butterrsoft/GyrSync/Code/main.c

/*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
 * THE SOFTWARE IS PROVIDED "AS IS", WITHOUT WARRANTY OF ANY KIND, EXPRESS OR
 * IMPLIED, INCLUDING BUT NOT LIMITED TO THE WARRANTIES OF MERCHANTABILITY,
 * FITNESS FOR A PARTICULAR PURPOSE AND NONINFRINGEMENT. IN NO EVENT SHALL THE
 * AUTHORS OR COPYRIGHT HOLDERS BE LIABLE FOR ANY CLAIM, DAMAGES OR OTHER
 * LIABILITY, WHETHER IN AN ACTION OF CONTRACT, TORT OR OTHERWISE, ARISING FROM,
 * OUT OF OR IN CONNECTION WITH THE SOFTWARE OR THE USE OR OTHER DEALINGS IN
 * THE SOFTWARE.
 */

/*
 * GyrSync dongle -- AVR32EB14. Composite sync combiner/converter.
 *
 * Built and verified with avr-gcc 16.1.0 (ZakKemble build), which has
 * avr32eb14/eb20 device support. Clean under -Wall -Wextra; also builds
 * for avr32eb20 unchanged, via `make MCU=avr32eb20`.
 *
 * ONE BUILD. There are no compile-time variants: no EXTRA, no
 * diagnostic switches, no alternative make targets that produce a
 * different image. `make flash` is the whole of it. The diagnostics
 * this file used to carry did their job and were removed with the
 * questions they answered -- and with them the class of fault they kept
 * causing, where a build selected on a command line reached the bench
 * without anything on the part to say which one it was.
 *
 * =====================================================================
 * WHERE THINGS LIVE
 * =====================================================================
 *
 * THE PIN MAP IS IN pins.h, AND ONLY THERE. It used to be duplicated in
 * this comment, and the copy drifted -- it described the pre-rotation
 * wiring, with DDC on pins 4/5 and Csync on pin 9, long after the
 * oscillator took PA0 and moved all of it. A map that disagrees with
 * itself is worse than no map, so there is one.
 *
 *   pins.h    every pin this project touches, named once
 *   clock.h   CLKCTRL, the PLL, the external oscillator
 *   tick.h    TCF0, the 4kHz interrupt and the millisecond tick
 *   evsys.h   all six event channels, and every event user
 *   ccl.h     all four LUTs, every truth table, CCLROUTEA
 *
 * Each of those modules is the SINGLE OWNER of its registers. That is
 * not tidiness: nearly every bug this firmware has had at the hardware
 * level was two writers on one register, and the split is what makes a
 * second writer a link error rather than a bench round.
 *
 * =====================================================================
 * PERIPHERAL ALLOCATION
 * =====================================================================
 *
 *   TCB0   Hsync capture, FRQ mode: one period measurement per line,
 *          restarted by the event system. Level 1 -- the only interrupt
 *          in this design that cannot be late, because Mode V counts
 *          lines and a lost count moves the emitted Vsync.
 *   TCB1   one timer, three jobs, one owner -- see tcb1_reevaluate().
 *          Mode S's pulse reshaping, the Hsync width measurement, and
 *          Mode FO's sub-line field delay.
 *   TCE0   the H offset. Restarted by Hsync in hardware, pulse placed
 *          by CMP0/CMP1 with the 8x high-resolution extension.
 *   TCF0   the 4kHz housekeeping interrupt: the millisecond tick and
 *          the Blink LED's software PWM.
 *   TWI0   the DDC/EDID client, at 0x50 with 0x30 also ACKed.
 *   CCL    the combiner and everything feeding it.
 *   RTC    unused.
 *
 * =====================================================================
 * THE Rev. A0 WRITE-LOSS ERRATUM, AND WHY NO WORK-AROUND APPEARS BELOW
 * =====================================================================
 *
 * A store to an address >= 0x40 followed by a store below 0x40 loses
 * the second write. Everything below 0x40 on this part is VPORTA/C/D/F
 * (0x00-0x17), GPR (0x1C) and the CPU block (0x30, which holds SREG and
 * the stack pointer). Every peripheral this firmware touches lives at
 * or above 0x40 -- PORT is at 0x0400, CCL at 0x01C0, and so on.
 *
 * So the rule is simply: NEVER TOUCH VPORT OR GPR. Use PORTx.OUTSET and
 * PORTx.OUTCLR, which are above the boundary and cannot be affected.
 * Nothing here needs VPORT's single-cycle access anyway -- the sync
 * path is combinational logic in the CCL, not the CPU.
 *
 * The one remaining sub-0x40 write is restoring SREG, which avr-gcc
 * emits as OUT -- itself the erratum's documented work-around. That is
 * a compiler behaviour rather than a guarantee, so `make lst` exists to
 * check it, and it should be re-checked whenever the toolchain changes.
 *
 * Checked on avr-gcc 16.1.0 for this build: every SREG access is
 * OUT 0x3f, CCP is OUT 0x34, the stack pointer is OUT 0x3d/0x3e, and
 * the only ST instructions in the image are the C runtime's .data copy
 * and .bss clear (targeting RAM at 0x7400+) and two inside
 * eeprom_update_byte (targeting the mapped EEPROM at 0x1400+ and
 * NVMCTRL at 0x1000+). Every one of those is at or above 0x40, so the
 * erratum's trigger condition does not occur anywhere in the build.
 */

#define F_CPU 20000000UL
#include "pins.h"
#include "tick.h"
#include "clock.h"
#include "evsys.h"
#include "ccl.h"

#include <avr/io.h>
#include <avr/interrupt.h>
#include <avr/eeprom.h>
#include <avr/cpufunc.h>   /* _PROTECTED_WRITE */
#include <string.h>        /* memcpy, for the EDID shadow rebuild */

/* THERE IS NO GENERATED EDID HEADER ANY MORE. edid_data.h is deleted.
 * The six images are the six .bin files, pulled straight into .rodata
 * by the assembler -- see the .incbin block in the DDC/EDID section
 * below, which is also where the build-time size rules live. */

/* ===================================================================
 * Modes
 * =================================================================== */

#define MODE_1  1
#define MODE_2  2
#define MODE_3  3
#define MODE_4  4
#define MODE_5  5
#define MODE_S  6

/* ===================================================================
 * Hsync acceptance windows, in TCB0 counts at CLK_PER
 * ===================================================================
 *
 * The fast and slow windows are carried over from the ATtiny824
 * unchanged. They are about 30% wide in frequency, so a half-percent of
 * oscillator error is nowhere near their edges and there is nothing to
 * recalibrate.
 *
 * Mode 4's window is the exception and is the one thing here that MUST
 * be re-measured on this part. It spans 24450-25450Hz, four percent
 * wide, which is close enough to the oscillator's own error that the
 * ATtiny824 build had to derive it from a bench measurement of that
 * chip -- ~19.897MHz rather than the nominal 20MHz -- before Mode 4
 * would accept a real 24960Hz source reliably.
 *
 * So Mode 4's edges are computed from F_PER_MEASURED rather than
 * written as counts, and nothing else in the file depends on the value.
 *
 * ON THE EXTERNAL OSCILLATOR THIS IS EXACT AND NEEDS NO CALIBRATION.
 * clock_init() runs the PLL from the 20MHz crystal module on pin 4, so
 * CLK_PER is 20MHz to the oscillator's 50ppm -- four hundred times
 * tighter than the four-percent window, and 20000000 is simply right.
 *
 * IT IS NOT EXACT ON THE FALLBACK PATH. If the oscillator is absent or
 * dead, clock_init() resets once and the second boot runs the PLL from
 * OSCHF instead, whose error is comparable to the width of this window
 * -- which is exactly why the ATtiny824 build had to measure its part
 * at ~19.897MHz before Mode 4 would accept a real 24960Hz source. A
 * unit that has fallen back may therefore reject Mode 4 sources it
 * should take. That is a consequence of a missing part rather than
 * something to trim this constant for: with the oscillator fitted,
 * leave it at 20000000.
 */
#define F_PER_MEASURED    20000000UL   /* <-- re-measure on the bench */

/* Boundaries land OUTSIDE the stated range in both directions: floor on
 * the low count, ceiling on the high one. An exactly-computed edge
 * rejects a legitimate source that misses it by a handful of counts. */
#define COUNTS_FLOOR(hz)  ((uint16_t)( F_PER_MEASURED / (hz)))
#define COUNTS_CEIL(hz)   ((uint16_t)((F_PER_MEASURED + (hz) - 1) / (hz)))

#define HSYNC_FAST_MIN_COUNTS   615   /* 32500Hz */
#define HSYNC_FAST_MAX_COUNTS   656   /* 30500Hz */
#define HSYNC_SLOW_MIN_COUNTS  1176   /* 17000Hz */
#define HSYNC_SLOW_MAX_COUNTS  1333   /* 15000Hz */
#define HSYNC_M4_MIN_COUNTS    COUNTS_FLOOR(25450UL)
#define HSYNC_M4_MAX_COUNTS    COUNTS_CEIL(24450UL)

_Static_assert(HSYNC_M4_MIN_COUNTS > HSYNC_FAST_MAX_COUNTS,
               "Mode 4 window overlaps the fast window");
_Static_assert(HSYNC_M4_MAX_COUNTS < HSYNC_SLOW_MIN_COUNTS,
               "Mode 4 window overlaps the slow window");

#define W_FAST 0x01
#define W_SLOW 0x02
#define W_M4   0x04

/* Which windows each mode accepts. One table to check against the mode
 * documentation, rather than a branch chain that recomputes the same
 * three tests and then picks between them. */
static const uint8_t mode_windows[MODE_S + 1] = {
    0,                        /* index 0 unused */
    W_SLOW,                   /* MODE_1  15-17kHz */
    W_FAST,                   /* MODE_2  30.5-32.5kHz */
    W_FAST | W_SLOW,          /* MODE_3  both */
    W_M4,                     /* MODE_4  narrow ~25kHz */
    W_FAST | W_SLOW | W_M4,   /* MODE_5  all three */
    W_FAST | W_SLOW,          /* MODE_S  both; divides the fast one,
                               * from increment 3 */
};

/* ===================================================================
 * Mode S divide-by-2, and the CCL role swap
 * ===================================================================
 *
 * Mode S accepts both the slow and the fast window. On a slow source it
 * passes Hsync through like any other mode. On a fast one it halves it,
 * so an unbidden 31kHz fallback still shows on a 15kHz CRT.
 *
 * THE DIVIDER OUTPUT IS A TIMING REFERENCE, NOT A SYNC SIGNAL. A
 * flip-flop dividing by two produces a 50% square wave -- about 32us
 * high and 32us low at the resulting 15.7kHz -- which no sync separator
 * will lock to. Each rising edge of it therefore fires a one-shot that
 * emits a fixed-width pulse, and that pulse is what reaches the
 * combiner. This is easy to miss because the divider looks perfect on a
 * logic analyser and fails only at the display.
 *
 * RISING EDGES ONLY, which is worth stating because section 4 of the
 * spec says "each of its edges triggers a one-shot". Taken literally
 * that undoes the division: the square wave has 15.7k rising and 15.7k
 * falling edges per second, so firing on both puts 31.5k pulses per
 * second back on the output. TCB1 is left with EVCTRL.EDGE clear, which
 * triggers on positive edges only and gives one pulse per output line.
 *
 * 4.0us is close to the 4.7us analogue standard and comfortably inside
 * what a 15kHz separator expects. It is a fixed count rather than a
 * fraction of the period because at this point the output rate is known
 * to be in the 15-17kHz window by construction.
 *
 * The counter runs at CLK_PER, so one count is 50ns.
 */
#define RESHAPE_PULSE_COUNTS     80          /* 80 x 50ns = 4.0us */

_Static_assert(RESHAPE_PULSE_COUNTS * 50UL < 10000UL,
               "reshape pulse is wider than a sync pulse should ever be");

/* Which shape the CCL is currently built in. The boundary between the
 * two is NOT the mode -- it is Mode S's own fast/slow decision, so the
 * swap happens at the rate threshold rather than at a mode change.
 *
 * REWRITTEN FOR THE ROTATION. This block described the pre-rotation
 * assignment, where LUT1 was the combiner and LUT2 held the two
 * alternating jobs. Since the oscillator took PA0 and DDC took PC3, the
 * only CCL output pin left is PD6, so LUT2 is the OUTPUT STAGE and is
 * the combiner in every role. What alternates is LUT0/LUT1 and LUT3.
 * ccl.c's header carries the full table.
 *
 *   CCL_ROLE_PASSTHRU  LUT2 combines, taking Hsync straight from the
 *                      pin by event. LUT1 is the restart edge sense and
 *                      LUT3 the reconstruction XOR, both built but only
 *                      consulted by TCE0. Every mode except
 *                      Mode-S-on-a-fast-source.
 *   CCL_ROLE_RECON     the same, except LUT2 takes its H input from
 *                      LUT3 by LINK -- the rebuilt, offset pulse
 *                      instead of the pin. Engaged only when the H
 *                      offset is off centre.
 *   CCL_ROLE_DIVIDE    LUT0+LUT1 become SEQ0's J-K, halving a fast
 *                      source; LUT2 takes the reshaped pulse from TCB1
 *                      on IN2; LUT3 is disabled. Mode S on a fast
 *                      source only, and the H offset stands down here
 *                      -- the divider wins because without it there is
 *                      no picture at all, whereas without the offset
 *                      there is merely a mispositioned one.
 */
/* ccl_role_t moved to ccl.h with the module that acts on it. */

/* ===================================================================
 * H offset (increment 4b)
 * ===================================================================
 *
 * The reconstruction is the XOR of TCE0's WO0 and WO1 -- a pulse
 * spanning CMP0 to CMP1, so BOTH its edges come from compare matches
 * and neither is at BOTTOM. That is what earns the high-resolution
 * extension on both edges rather than one, and diag1 confirmed on
 * silicon that the two are stable relative to each other within 10-20ns.
 *
 * ENGAGED ONLY WHEN THE OFFSET IS OFF-CENTRE, and only while the
 * genlock holds lock. At the neutral setting, and any time lock is
 * lost, LUT1 goes back to the pin. A genlock failure therefore costs
 * the offset, not the picture -- which is the right way round for a
 * device whose whole job is to produce Csync.
 *
 * STEP SIZE is derived from the measured period rather than fixed, so a
 * step means the same fraction of a line at any rate, as section 6.4
 * requires. One step is the period in hi-res units divided by 1024:
 * 9 units at 15.7kHz, which is 56ns, about two thirds of a pixel on a
 * 640-wide active area. 114 steps either side of centre is +/-10.1% of
 * a line.
 *
 * The spec asks for +/-12% and this is a little less. The history is
 * that the range came down and the resolution went up together: 61
 * steps of 244ns originally, then 121 of 119ns, then 181 of 56ns at
 * +/-8%, now 229 of 56ns at +/-10% -- the step held while the travel
 * was extended. Sub-pixel throughout, and 229 still fits the byte the
 * setting is stored in.
 *
 * 228 divides exactly by the UI stride of 6, so the sweep lands on both
 * ends AND on centre, where the offset switches itself off.
 */
#define H_OFFSET_STEPS    229
#define H_OFFSET_DEFAULT  114

#define HOFF_STEP_SHIFT   10    /* step = per_hires >> 10 */

/* Steps moved per short press in Mode H. One step is 56ns -- two thirds
 * of a pixel -- which is the right STORED resolution but far too fine to
 * sweep by hand: 180 presses end to end. Six steps is 337ns a press,
 * about four pixels, and 180 divides exactly by 6 so the range lands on
 * both ends AND on centre, where the offset switches itself off.
 *
 * Keeping the stored value fine and the UI coarse means the feel can be
 * retuned without touching the placement arithmetic or the EEPROM
 * format. */
#define HOFF_UI_STRIDE    6

/* MEASURED CHARACTERISTIC: THE NEGATIVE SIDE'S FLOOR WAS THE
 * OSCILLATOR, AND IS NOT ANY MORE. Both halves are worth keeping --
 * the first is why the crystal was fitted, the second is what it did.
 *
 * ON OSCHF. Emitted edge spread against how far after the restart the
 * pulse is placed, measured on Csync with delayed sweep and infinite
 * persistence, source jitter independently confirmed at 5ns:
 *
 *     6.25us delay ->  50ns      (positive offsets live here)
 *    56.25us       -> 100ns
 *    61.5us        -> 135ns      (negative offsets live here)
 *
 * The 50ns is the restart quantising to CLK_PER and is unavoidable. The
 * excess grew with the delay -- about 87ns by 56us, some 1540 ppm of
 * the interval -- and it was not the placement, which is exact, nor the
 * compare registers, which do not move. It was the clock counting the
 * delay out: running CLK_MAIN straight from OSCHF with no PLL gave the
 * same figures, so not the 16x multiplication either, but OSCHF itself
 * -- an internal RC oscillator whose frequency wanders over the 1125
 * cycles a negative offset has to count.
 *
 * That bounded the negative direction on that hardware. Every negative
 * offset, however small, waits nearly a whole line -- there is no
 * benign region near centre -- so the whole of that side sat at
 * 110-135ns while the positive side sat at 50ns.
 *
 * ON THE CRYSTAL, WHICH IS NOW FITTED. A 20MHz oscillator module on
 * pin 4 jitters in picoseconds, so the same walk over 1125 cycles comes
 * to tens of picoseconds against the 87ns above. The negative side now
 * sits at the same 50ns quantisation floor as the positive one, and the
 * asymmetry this block used to describe as shipped is gone.
 *
 * WHAT IT COST, since the note that used to be here said it was not
 * worth paying. EXTCLK exists only on PA0, which was SDA -- so fitting
 * the oscillator moved DDC to PC2/PC3, took PC3 away from the CCL, and
 * forced Csync to PD6 with the LUT roles rotated: LUT2 combining, LUT3
 * reconstructing, LUT1 converting the edge. A board revision and a
 * substantial rewire. It was done, and the roles above are its result.
 *
 * A NOTE ON THE ASYMMETRY, so it is not revisited.
 *
 * The two directions are not symmetric and no machinery makes them so.
 * One way delays sync from an edge that has already arrived, so the
 * pulse lands early in its own line and carries only the 50ns restart
 * quantisation. The other needs sync EARLIER than the edge being
 * referenced, which does not exist -- so the pulse goes near the end of
 * the PREVIOUS line, and the gap to the content it precedes is a whole
 * source line period. Whatever the source's period does line to line
 * lands on the picture. Section 3.2 justified that case on the source
 * being exactly periodic; a real graphics card wanders.
 *
 * Moving the NEUTRAL setting into the delay range makes both directions
 * land in their own line. It was built, measured, and rejected -- for a
 * reason unrelated to jitter. Only the sync is regenerated here; the
 * picture information passes from source to display untouched. So a
 * neutral that is a delay MOVES THE PICTURE by default, and correcting
 * that means adjusting the source's modeline or the display's geometry.
 * If either is being adjusted, the H offset had no reason to exist: it
 * earns its place only by correcting position without touching them.
 *
 * So the neutral stays at zero delay, one direction is stable, and the
 * other carries the source's wander.
 */

/* Narrowest emitted pulse, after any truncation by the next restart.
 *
 * THIS SETS THE NEGATIVE-SIDE DEAD ZONE, and the mechanism is worth
 * stating because it looks like a bug from the outside.
 *
 * The emitted pulse occupies [d, d+w] and the next restart is at
 * per_hires. For it to fit at all, d must not exceed per_hires minus the
 * width that survives. Since d = per_hires + offset, a negative offset
 * smaller than that width leaves no room -- the position is pinned and
 * only the pulse narrows, so the picture does not move. The first few
 * presses off centre therefore do nothing visible.
 *
 * A FULL-WIDTH pulse would need the offset to exceed 4.7us, which is
 * fourteen presses of dead zone. Allowing truncation to 1.2us brings it
 * to under four, which is about the least that still leaves a pulse a
 * sync separator will trigger on reliably. Below roughly 1us the
 * separator starts hunting and the cure is worse than the symptom.
 *
 * It cannot be removed. Placing the pulse earlier than the reference
 * edge means going to the previous line, and there has to be room
 * before the next restart for the pulse to exist in. Only the positive
 * direction is free of it, because there the whole line lies ahead. */
#define HOFF_MIN_WIDTH    (8u * 24u)      /* 1.2us */


/* ===================================================================
 * Line-period bounds
 * ===================================================================
 *
 * WHAT USED TO BE HERE. Increment 4a built a free-running genlock: TCE0
 * kept at the line rate by a feed-forward-plus-PI loop, its phase
 * sampled in the capture ISR, its period steered by dithering PER
 * between two adjacent 50ns steps. It worked, and it was removed -- the
 * loop's own cost was 400ns of emitted edge spread against the 50ns of
 * restart quantisation it existed to avoid. TCE0 is restarted by Hsync
 * in hardware now, and the H offset engine further down carries the
 * whole argument.
 *
 * Fifteen GENLOCK_* constants and about a hundred and twenty lines
 * describing that loop -- dither ratios, lock windows, outlier
 * rejection, why the proportional term was not optional -- outlived it
 * by several increments. THIRTEEN OF THE FIFTEEN WERE REFERENCED BY
 * NOTHING AT ALL, so the file read as though a control loop were still
 * in the signal path. They are gone.
 *
 * THE TWO SURVIVORS WERE NEVER ABOUT GENLOCK, which is why they
 * survived and why they are renamed. They bound the measured line
 * period: anything outside is not a rate this product serves, and
 * clamping stops a transient dragging the running average somewhere it
 * cannot walk back from. period_average() and hoffset_apply() are the
 * only readers. */
#define LINE_PER_MIN           600   /* ~33kHz */
#define LINE_PER_MAX          1400   /* ~14kHz */

/* ===================================================================
 * CCL truth tables
 * ===================================================================
 *
 * LUT1's truth index is IN2:IN1:IN0 = gate:Hsync:Vsync.
 *
 * The output is gate AND XNOR(Vsync, Hsync): high when the two syncs
 * agree, held low -- the muted state -- whenever the gate is low.
 *
 *   index 4 (gate=1, H=0, V=0) -> 1
 *   index 7 (gate=1, H=1, V=1) -> 1        = 0x90
 *
 * Inverting BOTH inputs of an XNOR leaves it unchanged, so the absolute
 * polarity of either sync is irrelevant -- only whether they AGREE.
 * That is why flipping one input's sense covers all four polarity
 * combinations, and why the whole polarity feature is a choice between
 * two truth-table values with no extra LUT, pin, timer or event
 * channel. Inverting one input of an XNOR makes it an XOR:
 *
 *   index 5 (gate=1, H=0, V=1) -> 1
 *   index 6 (gate=1, H=1, V=0) -> 1        = 0x60
 *
 * The output is idle-high and pulses low on either sync in both cases,
 * i.e. standard negative composite sync whatever the source did.
 */


/* --- H offset state ------------------------------------------------ */
static uint8_t  hoffset_running;
static uint8_t  h_offset = H_OFFSET_DEFAULT;
static uint16_t last_width_counts;      /* sync pulse, measured by TCB1 */

/* THE CAPTURE IS BACK IN AN INTERRUPT, and this time for a reason that
 * polling cannot satisfy.
 *
 * Polling was fine while nothing counted lines: a missed capture only
 * delayed a period measurement that was averaged anyway. Mode V counts
 * lines, and every lost capture moves the emitted Vsync -- which is a
 * jittering picture. The same loss also destabilised the frame length
 * and, earlier, glitched the mode-valid pin during DDC reads.
 *
 * An interrupt cannot miss one. It stays minimal: read the period,
 * advance the line, place the pulse if it is due, flag the main loop.
 *
 * NOTE FOR ANYONE REMOVING THIS: the ISR and the INTCTRL enable must
 * arrive and depart TOGETHER. An enabled interrupt with no handler
 * vectors to __bad_interrupt, which jumps to address zero -- the first
 * capture then resets the part, forever, with no other symptom.
 */
/* Lines since the frame boundary. WRITTEN ONLY IN THIS INTERRUPT -- see
 * the note on v_frame_req below. */
static uint16_t v_line;
static uint16_t v_prev_lines;
static void v_line_tick(void);
static void v_frame_start(void);

/* The main loop reads this to decide whether the regeneration may
 * engage at all. It is the only piece of Mode V's state that crosses out
 * of the capture interrupt -- and it is only ever tested against zero,
 * where a torn read of a 16-bit line count cannot turn zero into
 * non-zero or the reverse in any way that matters for one loop pass. So
 * it needs volatile and nothing more. */
static volatile uint16_t v_frame_lines;

/* Frame-referenced line counting, for an interlaced source. Declared
 * here, beside the interrupt that reads it, rather than in the Mode V
 * block that owns everything else.
 *
 * v_ilace is adopted at a frame boundary rather than the moment the
 * main loop decides it, so a change cannot land halfway through a
 * count; v_ilace_want is where the main loop leaves it.
 *
 * v_next_is_mid is a PREDICTION. The Vsync ISR cannot work out a
 * field's parity for itself -- that needs the phase weighed against the
 * line period, which is main-loop work -- so the main loop names the
 * next field instead, on the grounds that fields alternate. */
static uint8_t v_ilace;
static uint8_t v_ilace_want;
static uint8_t v_next_is_mid;

/* THE REFERENCE IS HELD BY ALTERNATION, NOT RE-MEASURED EVERY FIELD.
 *
 * Fields alternate, so once the right one has been identified the next
 * is simply the one after next. Re-deciding it from the measurement
 * every frame looked equivalent and was not: src_track_interlace's
 * mid-line window covers only the middle quarter of a line, and a source
 * whose phase sits near either edge of it will misread the odd field.
 *
 * The interlace DETECTOR survives that -- it has four-alternation
 * hysteresis, which is why the indicator reads steady. The reference
 * selection had none, so one misread field either skipped a reference
 * (the counter ran an extra frame into the runaway guard) or inserted a
 * spare one (the count came back a field short and was rejected). Both
 * destroy the believed frame length, and with it the position of the
 * second pulse -- leaving the two pulses 262 and 263 lines apart on
 * alternate frames instead of 262.5 each. A one-line shift at field
 * rate, which is a picture that jumps, and enough to stop a set locking,
 * which is a picture that rolls.
 *
 * So the measurement is consulted only while ACQUIRING, when there is no
 * frame length to lose. After that the alternation carries it, and a
 * misread field costs nothing. v_bad_frames drops back to acquisition if
 * the alternation itself is ever wrong, which is what a genuinely lost
 * Vsync edge would do. */
static uint8_t v_field_toggle;   /* flips on every field */
static uint8_t v_ref_parity;     /* the alternation carrying the reference */
static uint8_t v_bad_frames;     /* consecutive rejected frame counts */
#define V_BAD_FRAMES_MAX 4

/* WHERE THE REFERENCE IS, RELATIVE TO WHERE IT SHOULD BE, in lines.
 *
 * v_line is zeroed by the first capture that sees v_frame_req set by
 * the Vsync pin interrupt. The capture is level 1 and the Vsync
 * interrupt is level 0, so on a PROGRESSIVE source -- where the Vsync
 * edge is on the line grid and coincident with an Hsync -- the capture
 * can preempt the Vsync interrupt and read the flag before it has been
 * written. The reset is then deferred a whole line, and the emission,
 * which is placed a number of lines after that reset, moves with it.
 *
 * MEASURED, not deduced. A diagnostic build once held pin 11 high for
 * any frame whose line count disagreed with the last, and on the bench
 * it showed a uniform 50ms pulse -- three frames at 16.65ms --
 * coincident with every visible tic in the picture. Three frames is the
 * signature of exactly this: the deferred frame counts L+1, the next
 * counts L-1, and the third is back to L.
 *
 * The interlaced path does not suffer it, because its reference is the
 * MID-LINE field, whose Vsync edge sits half a line from any Hsync.
 * The comment in the capture interrupt says so and is still live; a
 * progressive source simply has no mid-line field to choose.
 *
 * WHAT DECIDES THE RACE IS STILL UNKNOWN. Two candidates have been
 * measured and eliminated: DDC traffic delaying the level 0 interrupt
 * (turning EDID off changes nothing) and source jitter flipping which
 * edge lands first (Hsync jitter measures 5ns, which could only matter
 * if the two edges were already within 5ns of each other). Do not
 * guess at a third here. This accumulator does not need to know: it
 * removes the emission's DEPENDENCE on the attribution rather than
 * fixing the attribution.
 *
 * CUMULATIVE, AND THAT IS THE WHOLE POINT. The per-frame difference is
 * the wrong quantity. A frame counting L+1 says the reference has moved
 * one line late; the L-1 frame that follows says it has moved back, and
 * correcting THAT one would introduce an error where there was none.
 * Only the running total describes where the reference actually is.
 *
 * Clamped because a believed frame length that is wrong by one would
 * otherwise accumulate a line every frame and walk the picture off the
 * screen. With the stability test now requiring exact agreement that
 * should not happen, so the clamp is a bound on the damage rather than
 * a working part -- but it is the difference between a defect and a
 * runaway. */
static int8_t v_slip;
#define V_SLIP_MAX 4

/* A line count this far past any legitimate frame means the reference
 * was missed. On an interlaced source only one field in two resets the
 * counter, so losing that field's edge would let it run until it
 * wrapped. The widest legitimate frame here is a 45Hz field on a 17kHz
 * interlaced source, about 760 lines. */
#define V_LINE_RUNAWAY 1000

/* THE FRAME BOUNDARY IS A REQUEST, NOT AN ACTION, and promoting this
 * capture to level 1 is what forces that.
 *
 * The Vsync interrupt used to reset the line count and compute the
 * emission point itself. At level 0 for both that was safe, because
 * neither interrupt could interrupt the other. At level 1 this one CAN
 * land in the middle of the Vsync ISR, and v_line, v_start_line and
 * v_frame_lines are all 16-bit: a capture arriving between the two
 * stores of a 16-bit write gives a torn read, and a torn v_start_line
 * puts that frame's Vsync somewhere arbitrary. Which is a picture that
 * jumps once every few seconds -- the hardest kind of fault to catch,
 * because it looks like a source problem.
 *
 * Masking this interrupt across the Vsync ISR is the obvious fix and is
 * the WRONG one. The mask would be about 1.5us against a 63.6us line, so
 * one frame in forty loses the very count the mask exists to protect,
 * and the emission point moves by a line -- which is precisely the
 * jitter being chased.
 *
 * So the Vsync ISR sets an 8-bit flag and nothing else, and the frame
 * boundary is done HERE, on the next capture. Every variable Mode V
 * touches then lives in one interrupt context and there is nothing left
 * to tear. The cost is that the count resets on the first Hsync after
 * Vsync rather than at the Vsync edge, which is the resolution the whole
 * scheme works at anyway -- and it is the same quantisation the +/-1
 * line frame-length test already absorbs. */
static volatile uint8_t  v_frame_req;
static volatile uint8_t  v_frame_req_mid;   /* was that field mid-line? */

static volatile uint16_t cap_period;
static volatile uint8_t  cap_ready;

ISR(TCB0_INT_vect)
{
    uint16_t period = TCB0.CCMP;      /* clears CAPT; already restarted */
    cap_period = period;
    cap_ready  = 1;

    if (v_frame_req) {
        v_frame_req = 0;

        /* ON AN INTERLACED SOURCE ONLY ONE OF THE TWO FIELDS RESETS THE
         * COUNTER -- the mid-line one, whose Vsync edge sits squarely
         * half a line from any Hsync, so the capture that follows it is
         * never in doubt. The on-grid field's edge is coincident with an
         * Hsync and the race between them can be decided differently
         * from one frame to the next. Using it as the reference would
         * put a whole line of jitter into the very measurement the
         * reconstruction is built on. */
        if (!v_ilace) {
            v_frame_start();
        } else {
            v_field_toggle ^= 1;

            if (!v_frame_lines) {
                /* Acquiring. Nothing to lose, so take the measurement
                 * and remember which alternation it landed on. */
                if (v_frame_req_mid) {
                    v_ref_parity = v_field_toggle;
                    v_frame_start();
                }
            } else if (v_field_toggle == v_ref_parity) {
                v_frame_start();
            }
        }
    }

    v_line++;

    /* A missed reference must not be allowed to run away. On an
     * interlaced source the counter is reset by one field in two, so
     * losing that field's edge means nothing resets it until the count
     * wraps at 65535 -- by which time the frame length has been rejected
     * for hundreds of frames and the picture is gone. Invalidating the
     * length forces the stability test to re-earn it from scratch. */
    if (v_line > V_LINE_RUNAWAY) {
        v_line        = 0;
        v_prev_lines  = 0;
        v_frame_lines = 0;
    }

    v_line_tick();
}

/* Old note, kept because the reasoning still applies to everything the
 * main loop does with the captured value:
 *
 * It was moved into an interrupt so the genlock could sample TCE0.CNT
 * at a known point after the Hsync edge. Nothing needs that now -- the
 * restart is done by the event system, in hardware -- and the period
 * measurement this feeds is used for window checking and for scaling
 * the offset step, neither of which cares whether a line is missed. */


/* ===================================================================
 * Timing constants, in 1ms ticks
 * =================================================================== */

#define POL_SAMPLE_TICKS         20   /* idle-level sample window.
                                       *
                                       * Polarity is a majority vote on
                                       * a DC property present 98-99% of
                                       * the time, not a hunt for a rare
                                       * event, so it does not need to
                                       * span a frame. 20ms at one
                                       * sample per loop pass is
                                       * thousands of samples with a
                                       * 99:1 margin, and keeping it
                                       * short is what lets the mute
                                       * come down to 40ms. */
#define SETTLE_TICKS_SOURCE     220   /* Csync and the Mode-Valid LED
                                       * muted after the SOURCE changes
                                       * its line rate, as opposed to
                                       * after something this firmware
                                       * did. Long because the mute has
                                       * to outlast a graphics card's
                                       * whole modeline transition --
                                       * measured at 200ms worst case --
                                       * and it retriggers on each step
                                       * within it. Both are muted: the
                                       * LED blinking through a change
                                       * is the reported symptom, the
                                       * output unmuting into a
                                       * transient mode is the part
                                       * that reaches the display. */

#define BOOT_SETTLE_TICKS       250   /* Csync and the Mode-Valid LED
                                       * muted from reset until
                                       * acquisition has finished
                                       * churning. ONE CURTAIN OVER THE
                                       * WHOLE OF IT, rather than a
                                       * settle per event.
                                       *
                                       * THE FAULT THIS CLOSES. A
                                       * profile with the H offset off
                                       * centre strobed the Mode-Valid
                                       * LED at every power-on: two or
                                       * three mutes of about 60ms with
                                       * brief valid windows between
                                       * them, worst at 15kHz. Isolated
                                       * on the bench by centring the
                                       * offset, which removed it.
                                       *
                                       * EVERY ONE OF THOSE MUTES WAS
                                       * INDIVIDUALLY CORRECT. The CCL
                                       * really was being reconfigured
                                       * each time and muting across a
                                       * reconfiguration is right. What
                                       * was wrong is that they arrived
                                       * as a strobe. A display's PLL
                                       * cares far more about sync
                                       * appearing, vanishing and
                                       * reappearing than about sync
                                       * arriving late once, so the fix
                                       * is to hide the churn rather
                                       * than to remove any one settle.
                                       *
                                       * WHAT HAPPENS UNDERNEATH, traced
                                       * with pin 11 over four
                                       * diagnostic builds. The source
                                       * terms never drop -- hsync_valid
                                       * and field_rate_ok are innocent
                                       * and the watchdog never fires.
                                       * h_pin_idle_high moves once, off
                                       * its BSS zero, which is real
                                       * work. pol_flip then moves TWICE
                                       * more, 0->1 at 25ms and 1->0 at
                                       * 85ms, each inside a mute that
                                       * was already up and each
                                       * followed 40ms later by that
                                       * mute lifting. So
                                       * polarity_measure() raises them,
                                       * and want_flip is being computed
                                       * against acquisition state that
                                       * is still moving: the CCL role,
                                       * and fo_active, both of which
                                       * force a term of want_flip and
                                       * both of which settle at their
                                       * own pace.
                                       *
                                       * 250 AGAINST A WORST OBSERVED
                                       * 220. The longest boot churn
                                       * measured was low 0-60, high
                                       * 60-160, low 160-220, at 15kHz
                                       * with the H offset engaged and
                                       * Mode FO disengaged. That is
                                       * 30ms of margin and no more, so
                                       * it is a number to re-measure
                                       * rather than to trust: if any
                                       * event behind this curtain ever
                                       * scales with the source -- the
                                       * interlace detector counts
                                       * FRAMES, for one -- a slower
                                       * source could outrun it, and the
                                       * symptom would return quietly as
                                       * a single late pulse rather than
                                       * as the obvious strobe.
                                       *
                                       * Longer than SETTLE_TICKS_SOURCE
                                       * deliberately: a modeline change
                                       * mid-run has a settled firmware
                                       * underneath it, and boot does
                                       * not. */

#define SETTLE_TICKS             40   /* Csync muted while the firmware
                                       * decides something: the 20ms
                                       * polarity measurement, during
                                       * which the output is still being
                                       * combined with the PREVIOUS
                                       * modeline's polarity, plus the
                                       * rebuild that may follow it. */
#define HSYNC_WATCHDOG_TICKS      3   /* captures stopped arriving.
                                       *
                                       * MUST BE AT LEAST 2, and the
                                       * reason is tick quantisation
                                       * rather than the signal. A tick
                                       * boundary can fall immediately
                                       * after a capture, so an elapsed
                                       * count of N guarantees only
                                       * (N-1) ms of real time. At 1 the
                                       * watchdog therefore fires with
                                       * no time elapsed at all, once
                                       * per tick, forever -- see the
                                       * note in the main loop for what
                                       * that then wrecks.
                                       *
                                       * 3 guarantees at least 2ms, i.e.
                                       * 30 missed lines at 15kHz and 62
                                       * at 31kHz. Sync is gone, not
                                       * late, and a real dropout is
                                       * still caught within 3ms. */
/* TWO CONSTANTS, BECAUSE THERE ARE TWO JOBS.
 *
 * The whole history of this debounce is one constant being asked to do
 * both, and failing whichever way it was turned: long enough to outlast
 * bounce was long enough to swallow a real second press (the merge),
 * short enough to pass real presses was short enough for bounce to look
 * like one (the split). Then trusting a single sample fixed both and
 * let electrical noise in instead. Three failures, one cause.
 *
 * B1_QUALIFY_MS -- NOISE. How long the pin must hold the new level
 * CONTINUOUSLY before the edge is believed. Sampled at loop rate, which
 * is many times per millisecond, so this is thousands of consecutive
 * samples and any glitch shorter than it resets the count. Set to 8,
 * deliberately identical to the old DEBOUNCE_TICKS, because that build
 * ran on the bench without phantom presses and matching it exactly is
 * the only claim about noise that can be made without a scope on the
 * pin. It is NOT a bounce filter and must stay short: it is the floor
 * on the gap between two real presses, and at 8ms no finger can trip it.
 *
 * B1_LOCKOUT_MS -- BOUNCE. Dead time after an edge has been ACCEPTED,
 * during which nothing is looked at. This is what outlasts contact
 * settling, and it can be generous precisely because it no longer has
 * to pass real presses -- it starts after the edge is already believed,
 * so a second press inside it is delayed rather than lost.
 *
 * THE SEPARATION IS THE FIX. Neither number can reintroduce the other's
 * failure, which is what no single value could manage. */
#ifndef B1_QUALIFY_MS
#define B1_QUALIFY_MS             8
#endif
#ifndef B1_LOCKOUT_MS
#define B1_LOCKOUT_MS            25
#endif

/* ===================================================================
 * Held-button timeline (section 8.1 unlocked, 8.1a locked)
 * ===================================================================
 *
 * Each indication says what releasing NOW will do. The two Mode S codes
 * and the gap around them mark the MS window; the fast 150ms blinks mark
 * the lockout window; and the LED going DARK at the end is the last
 * warning before something destructive.
 *
 * The locked timeline is the same shape on a shorter scale, so the
 * gesture is learned once: nothing at all, then fast blinks, then dark.
 */
#define HOLD_PROFILE1_MS      2000     /*  2-4s   profile 1               */
#define HOLD_PROFILE2_MS      4000     /*  4-6s   profile 2               */
#define HOLD_PROFILE3_MS      6000     /*  6-8s   profile 3               */
#define HOLD_MS_ENTER_MS      8000     /*  8-11s  Mode S                  */
#define HOLD_CS_ENTER_MS     11000     /* 11-13s  Mode CS                 */
#define HOLD_ED_ENTER_MS     13000     /* 13-16s  Mode ED                 */
#define HOLD_LOCK_MS         16000     /* 16-25s  button lockout          */
#define HOLD_FACTORY_MS      25000     /* 25s+    factory reset           */

/* THE ED WINDOW IS THREE SECONDS WIDE WHERE THE OTHERS ARE TWO, AND
 * THAT IS DELIBERATE. It sits at the deepest point of the ladder, where
 * nobody is still counting, and the thing immediately above it is the
 * lockout -- the most irritating window on the timeline to land in by
 * accident. Overshooting Mode ED costs a lockout and an unlock gesture;
 * overshooting Mode CS only costs a second attempt. So the margin is
 * spent on the side where a miss is expensive. Lockout still gets four
 * seconds, which is twice what it needs.
 *
 * THE LOCKOUT WINDOW IS NINE SECONDS WIDE, 16s TO 25s, AND FACTORY
 * RESET IS THE ONLY THING BELOW IT. It was 16s to 20s. Widening it
 * costs nothing -- nobody navigates TO the lockout by counting, they
 * arrive at it by watching the fast blinks start -- and it buys the
 * one thing the timeline could not otherwise give: distance in front
 * of the only gesture on the ladder that destroys settings.
 *
 * The blinks run the whole nine seconds, so the warning that something
 * irreversible is close is now the LED going dark at 25s rather than a
 * four-second window a slow hand can cross. Nothing else moves: the
 * locked ladder is a separate, shorter timeline and keeps its 10s.
 *
 * Both new windows are navigable by WATCHING rather than counting:
 * solid through the CS window, dark through the ED window, fast blinks
 * from the lockout. Two crisp transitions land exactly where the
 * counting has broken down. */
_Static_assert(HOLD_PROFILE1_MS < HOLD_PROFILE2_MS
            && HOLD_PROFILE2_MS < HOLD_PROFILE3_MS
            && HOLD_PROFILE3_MS < HOLD_MS_ENTER_MS
            && HOLD_MS_ENTER_MS < HOLD_CS_ENTER_MS
            && HOLD_CS_ENTER_MS < HOLD_ED_ENTER_MS
            && HOLD_ED_ENTER_MS < HOLD_LOCK_MS
            && HOLD_LOCK_MS     < HOLD_FACTORY_MS,
            "held-button timeline must be strictly increasing");

#define HOLD_L_UNLOCK_MS      3000     /* locked: 3-10s unlocks */
#define HOLD_L_FACTORY_MS    10000

/* Inside MS (section 8.2) */
#define HOLD_MODE_H_MS        2000
#define HOLD_MODE_V_MS        4000
#define HOLD_MODE_FO_MS       6000
#define MS_DOUBLE_MS           500     /* deferral window for a 2nd press */

/* Adjustment modes (section 8.3) */
/* Mode ED's in-mode ladder. Four bands where H/V/FO have three, because
 * the axis change needs one -- which is why 8s+ is not "reset and exit"
 * as it is in the other modes. Reset here changes the ACTIVE AXIS and
 * stays put; the only exits are save at 4-6s and the idle timeout. */
#define ED_REVERSE_MS         2000     /* solid    : reverse direction */
#define ED_SAVE_MS            4000     /* dark     : save both, exit   */
#define ED_RESET_MS           6000     /* solid    : reset active axis */
#define ED_AXIS_MS            8000     /* pulsing  : position <-> size */
#define ED_IDLE_MS           30000     /* 30s, not 20s                 */

#define ADJ_REVERSE_MS        2000
#define ADJ_SAVE_MS           4000
#define ADJ_RESET_MS          6000
#define ADJ_IDLE_MS          20000
#define ADJ_STROBE_MS         1200

#define POL_PERIOD_SHIFT          6   /* re-measure if the line period
                                       * moves by more than 1/64, ~1.6%
                                       * -- wider than measurement
                                       * noise, narrower than any real
                                       * modeline step */
#define POL_STREAK_REQUIRED       8   /* consecutive out-of-tolerance
                                       * periods before believing it.
                                       *
                                       * One sample is not enough, and
                                       * an interlaced source proves it:
                                       * the half line ending each field
                                       * is a genuinely short Hsync
                                       * period, once per field, every
                                       * field. A single-sample trigger
                                       * fires on it 120 times a second
                                       * forever. Any in-tolerance
                                       * period resets the count, so an
                                       * isolated anomaly can never
                                       * accumulate, while a real
                                       * modeline change -- where EVERY
                                       * period differs -- reaches 8 in
                                       * about half a millisecond. */

/* ===================================================================
 * EEPROM
 * ===================================================================
 *
 * 512 bytes here against 128 on the ATtiny824, so the layout was sized
 * for the whole feature set up front rather than grown a byte at a
 * time. All 25 are in use now. Unwritten bytes read 0xFF and every load
 * path range-checks, so growing into the remaining space costs nothing
 * and needs no magic bump -- which matters, because a bump discards the
 * settings that ARE in use.
 *
 * Each setting is written by persist_byte(), which commits only the
 * byte that changed plus the magic, written LAST. An interrupted write
 * can therefore never leave a valid magic vouching for a stale
 * companion.
 *
 * The magic is a LAYOUT VERSION, not a checksum. Bump it only when the
 * meaning of an existing byte changes. It starts fresh for the EB
 * rather than continuing the ATtiny824's sequence, since no EB part has
 * ever held the old layout and there is nothing to be compatible with.
 *
 * The bytes are one array rather than separate EEMEM symbols, because
 * the linker does not guarantee predictable relative placement between
 * separate EEMEM symbols -- confirmed with nm on the ATtiny824 build,
 * where the order came out looking alphabetical rather than as
 * declared. An array's layout is fixed by construction.
 */
#define MODE_MAGIC        0xE5   /* bumped: Mode CS method 3 inserted, 3-6 shifted to 4-7 */

/* Magic bumped whenever the layout or a setting's range changes, so a
 * part carrying an older layout discards it rather than reading stale
 * values as valid. Two changes have earned a bump so far: the H
 * offset's step count, which has moved several times on its way to the
 * 229 it holds now, and inserting Mode CS's method 3 rather than
 * appending it. Factory reset (section 8.1b) restores the same defaults
 * a freshly programmed part boots with. */
#define EE_MAGIC           0
#define EE_MODE            1
#define EE_B1_LOCKED       2
#define EE_PROFILE         3
#define EE_EDID_P1         4     /* per profile, +0 +1 +2 */
#define EE_HOFF_P1         7
#define EE_VOFF_P1        10
#define EE_FOFF_P1        13

/* ALLOCATED AHEAD OF THEIR CODE, AND NOW WRITTEN BY IT.
 *
 * Mode ED needs six bytes and Mode CS needs three. Landing them in two
 * separate increments would have meant two magic bumps and two wipes of
 * the user's settings, so the layout was grown ONCE and the bytes sat
 * unwritten until the code that owns them existed. It does now: Mode
 * ED's save gesture writes EE_EDPOS/EE_EDSIZE, Mode CS's writes
 * EE_CSMETH, and factory_reset() writes all three per profile.
 *
 * WHAT THAT COST, AND WHY IT WAS STILL THE RIGHT ORDER. The reservation
 * bought exactly one bump instead of two, and the bump it could not
 * avoid was spent elsewhere -- inserting Mode CS's method 3 rather than
 * appending it moved the meaning of a stored in-range value, which is
 * precisely what section 14 requires a bump for. MODE_MAGIC is 0xE5.
 *
 * The rule these slots were reserved under still applies to whatever is
 * added next: an erased byte is 0xFF, every loader below range-checks,
 * and 0xFF is out of range for any range -- so growing INTO unwritten
 * bytes needs no bump. Changing the meaning of a written one does. */
#define EE_EDPOS_P1       16     /* Mode ED  horizontal position, per profile */
#define EE_EDSIZE_P1      19     /* Mode ED  horizontal size,     per profile */
#define EE_CSMETH_P1      22     /* Mode CS  combine method,      per profile */
#define EE_BYTES          25

#define PROFILE_COUNT      3
#define PROFILE_DEFAULT    1

/* Offsets are stored as unsigned step indices with the middle as the
 * neutral setting, exactly as on the ATtiny824. */
#define V_OFFSET_STEPS    61
#define V_OFFSET_DEFAULT  30
#define F_OFFSET_STEPS    31
#define F_OFFSET_DEFAULT  15

static uint8_t EEMEM eeprom_data[EE_BYTES];

static void persist_byte(uint8_t idx, uint8_t value)
{
    eeprom_update_byte(&eeprom_data[idx], value);
    eeprom_update_byte(&eeprom_data[EE_MAGIC], MODE_MAGIC);
}

/* ===================================================================
 * State
 * =================================================================== */

static uint8_t  current_mode  = MODE_1;
static uint8_t  current_profile = PROFILE_DEFAULT;
static uint8_t  edid_enabled;
static uint8_t  b1_locked;

static uint8_t  hsync_valid;          /* period inside the mode's window */
static uint8_t  mode_valid;           /* what the gate pin is driving */
static uint16_t last_period_counts;
static uint8_t  last_windows;
static uint16_t last_hsync_tick;

/* ccl_role lives in ccl.c now; read it with ccl_current_role(). */


static uint8_t  pol_flip;             /* 1 -> LUT1 uses XOR, not XNOR */
static uint8_t  h_pin_idle_high = 1;  /* the source's own Hsync sense */

/* Which edge of the incoming pulse restarts TCE0. One function decides
 * it, so the two places that write the edge sense's TRUTH1 cannot
 * disagree. */
static uint8_t  pol_pending = 1;      /* measure once at start-up */

/* A RE-MEASURE THAT DOES NOT MUTE.
 *
 * pol_pending both measures and blanks the output, which is right when
 * the combiner's inputs have just changed identity -- a mode change, a
 * role change -- because what it was emitting is no longer meaningful.
 *
 * But a source flipping its sync polarity changes NOTHING that any
 * existing trigger watches. The period is identical, so the modeline
 * detector stays quiet, and the stale polarity holds until something
 * unrelated happens to force a measurement. That is exactly the
 * "sometimes it works" behaviour: whether the picture is right depends
 * on whether anything else disturbed the unit since the polarity moved.
 *
 * So this runs the same measurement on a timer without blanking.
 * polarity_measure only applies a change when the answer actually
 * differs, so a recheck that finds nothing costs a truth-table
 * comparison and no visible interruption. */
#define POL_RECHECK_MS   250
static uint8_t  pol_recheck;
static uint16_t pol_recheck_at;

/* Separate from pol_pending, and it has to be.
 *
 * The genlock's re-acquisition used to be triggered by pol_pending, on
 * the reasoning that the one event justifying a restart -- a modeline
 * change -- announces itself as a polarity re-measure. That held until
 * something else started asking for a polarity re-measure: switching
 * the CCL role changes the H input's idle level from the pin's to a
 * regenerated one, so it must re-measure, and it set the same flag.
 *
 * The result was a standoff. Engaging the reconstruction set
 * pol_pending; pol_pending restarted the genlock; the restart cleared
 * lock; and the reconstruction is only used while locked, so the role
 * fell straight back and set the flag again. It cycled once per line
 * and lock was never held for the 64 lines it needs, so the offset
 * never took effect at all.
 *
 * It also explains something from before 4b: pol_pending stays set for
 * the whole 20ms polarity measurement, and nothing cleared it in the
 * restart branch, so every one of those measurements was restarting
 * the genlock on every line throughout. */
static uint8_t  genlock_reacquire;
static uint8_t  pol_measuring;
static uint16_t pol_start;
static uint16_t pol_h_high, pol_h_low;
static uint16_t pol_v_high, pol_v_low;

/* Vsync presence, for the section 8.2 sync report.
 *
 * Hsync has the capture timer and its watchdog; Vsync has neither, and
 * the polarity counters are no substitute -- they run for 20ms, which is
 * about one field, so a single missed pulse reads as absence.
 *
 * Watching for ANY edge and allowing 100ms without one covers every
 * field rate down to 10Hz, well below anything this will ever see, and
 * needs no assumption about polarity or duty. */
static volatile uint16_t field_qtick;     /* qtick at the last frame edge */
static volatile uint16_t field_period_q;  /* last interval, quarter-ms */
static uint8_t  field_bad;
static uint8_t  field_rate_ok = 1;  /* absent Vsync passes */

static uint16_t vs_change;
static uint8_t  vsync_present;

/* ===================================================================
 * Interlace detection (section 9)
 * ===================================================================
 *
 * An interlaced source alternates: one field's Vsync sits ON the line
 * grid, the next lands in the MIDDLE of a line. So the test is simply
 * where the Vsync edge falls within a line, and whether that answer
 * toggles frame to frame. A progressive source reports the same phase
 * every frame and so reports no interlace.
 *
 * PHASE COMES FREE from TCB0. In frequency mode the counter restarts on
 * every Hsync edge, so its value at the Vsync edge IS the elapsed time
 * since the last line started -- provided it is read AT the edge, which
 * is why this needs an interrupt rather than the polling that serves
 * presence detection.
 *
 * THE MIDDLE QUARTER, not the middle half. Testing between 3/8 and 5/8
 * of a line keeps the decision boundaries away from 25% and 75%, which
 * is where a real Vsync phase can plausibly sit -- and there a few
 * microseconds of interrupt jitter flips the answer every frame.
 *
 * FOUR ALTERNATIONS TO LATCH, EIGHT AGREEMENTS TO RELEASE. Interlace
 * alternates every frame, so a sustained run says so in four. Latching
 * on a single disagreement means one jittery reading pins a progressive
 * source as interlaced -- and if the jitter recurs more often than the
 * release window it never clears, which is why Mode FO would not lock
 * out on a progressive source.
 */
/* ===================================================================
 * The two regenerated Vsync paths, and why they cannot both be on
 * ===================================================================
 *
 * Mode V substitutes a Vsync it emits on pin 13, quantised to the line
 * grid. Mode FO leaves the source's Vsync where it is and delays ONE
 * FIELD of it by a fraction of a line.
 *
 * v_regen requires a PROGRESSIVE source and fo_active requires an
 * INTERLACED one, so the two are mutually exclusive by construction --
 * not by a rule written somewhere that could be forgotten. That is what
 * section 7 means when it says the two are exclusive on the ATtiny824,
 * and it is why the awkward case (a line-quantised pulse that has to
 * have half a line put back into it before a field offset means
 * anything) does not arise here at all.
 *
 * The code below still asks which source LUT0 is looking at rather than
 * assuming the pin, because the combination is the one thing section 7
 * asks for later and the question will become live. */
static uint8_t v_regen;            /* 1 -> the V source is pin 13 */

static uint8_t fo_active;          /* 1 -> LUT0's field delay is in path */

/* The source's OWN Vsync sense, kept separately from the value the
 * combiner is given -- exactly as h_pin_idle_high is for Hsync. LUT0
 * needs it to know which way round to build its truth table, and that
 * is a property of the source, not of the path Csync currently takes. */
static uint8_t v_pin_idle_high = 1;

/* Set where the SYNC WIDTH could have changed, and nowhere else.
 *
 * The first attempt hung the width burst off pol_pending, which was
 * wrong in a way worth recording because it locks up outright rather
 * than merely misbehaving. Engaging Mode FO changes what the combiner
 * sees, so it sets pol_pending; pol_pending would start a width burst;
 * the burst takes TCB1 away, so Mode FO stands down; standing down
 * changes the routing back, which sets pol_pending again. Twenty
 * milliseconds a cycle, forever, with Csync muted throughout -- because
 * pol_pending is gated into mode_valid.
 *
 * A flag that means "the width may have changed" cannot be the same flag
 * as "the combiner's inputs may have changed sense". They share most of
 * their causes and differ in exactly the one that matters. */
static uint8_t width_pending = 1;   /* measure once at start-up */

/* Set while the polarity window has borrowed TCB1 back to measure the
 * sync width. Mode FO stands down for its duration -- see fo_update(). */
static uint8_t width_burst;

/* Mode FO reloads TCB1's delay once per field, deferred a couple of
 * milliseconds from the Vsync edge that arms it -- see
 * fo_load_service(), which explains why it cannot be done at the edge. */
static uint8_t  fo_load_pending;
static uint16_t fo_load_at;

static uint8_t  src_prev_mid;
static uint8_t  src_alt_count;
static uint8_t  src_prog_count;
static uint8_t  src_interlaced;

static volatile uint16_t vs_phase;      /* TCB0.CNT at the leading edge */
static volatile uint8_t  vs_frame_flag; /* a frame boundary was latched */
static volatile uint8_t  vs_any_edge;   /* any edge, for presence */

/* Runs in the main loop from the flag the ISR sets, because none of it
 * is urgent and the ISR must stay short enough not to disturb DDC. */
static void src_track_interlace(uint16_t phase)
{
    uint16_t p = last_period_counts;
    if (!p) return;

    uint8_t midline = (phase > (uint16_t)((p >> 2) + (p >> 3))
                    && phase < (uint16_t)((p >> 1) + (p >> 3))) ? 1 : 0;

    if (midline != src_prev_mid) {
        if (src_alt_count < 4 && ++src_alt_count >= 4) src_interlaced = 1;
        src_prog_count = 0;
    } else {
        src_alt_count = 0;
        if (src_prog_count < 8 && ++src_prog_count >= 8) src_interlaced = 0;
    }
    src_prev_mid = midline;
}

/* Vsync edge interrupt. Deliberately tiny: capture the phase before the
 * counter moves on, note the level, flag it, leave. Everything that can
 * wait is done in the main loop. */
ISR(PORTC_PORT_vect)
{
    if (PIN_VSYNC_PORT.INTFLAGS & PIN_VSYNC_bm) {
        /* THE 16-BIT READ IS MASKED, and this is not paranoia.
         *
         * A 16-bit peripheral register is read low byte first, which
         * latches the high byte into that PERIPHERAL'S shared TEMP
         * register; the high byte then comes from TEMP. The capture
         * interrupt is level 1 and reads TCB0.CCMP, the same
         * peripheral's TEMP. Landing between these two bytes replaces
         * CNT's high byte with CCMP's -- a phase reading of a thousand
         * counts where it should have been ten, which is the difference
         * between a mid-line field and an on-grid one.
         *
         * Masking cannot lose a capture: the flag stays set and the
         * handler runs the moment it is unmasked, six cycles later. */
        TCB0.INTCTRL   = 0;
        uint16_t phase = TCB0.CNT;
        TCB0.INTCTRL   = TCB_CAPT_bm;

        uint8_t  lvl   = (PIN_VSYNC_PORT.IN & PIN_VSYNC_bm) ? 1 : 0;

        /* THE FRAME BOUNDARY IS LATCHED HERE, not deferred.
         *
         * A flag cannot carry it. This fires on BOTH edges, and a short
         * Vsync pulse gives both between two main loop passes -- so the
         * rising edge is overwritten before it is read, that frame's
         * line count is never latched, and the next frame counts two
         * frames' worth. The rate check then rejects a perfectly good
         * mode for one field, which is Csync dropping out in bursts.
         *
         * Latching in the interrupt cannot lose an edge. The line
         * counter is now advanced by the capture interrupt rather than
         * by the main loop, so it cannot lose a count in the race
         * either. */
        if (lvl) {
            vs_phase         = phase;
            /* Interval since the previous frame edge, in QUARTER-
             * milliseconds. Taken here in the interrupt so it is a real
             * frame boundary, not whenever the main loop next looked.
             *
             * qtick_count rather than tick_count, and the plain read is
             * safe for the same reason it was there: this handler and
             * TCF0 are both level 0, so neither can land inside the
             * other's 16-bit access. See tick.h, which offers no
             * accessor precisely so that rule has to be read. */
            uint16_t t = qtick_count;
            field_period_q = (uint16_t)(t - field_qtick);
            field_qtick    = t;
            /* REQUESTED, not performed. This ISR is level 0 and the
             * capture is level 1, so doing the frame work here would put
             * 16-bit writes where a capture can land between their two
             * stores. See the note at the capture ISR. */
            v_frame_req      = 1;
            v_frame_req_mid  = v_next_is_mid;
            vs_frame_flag    = 1;
        }
        vs_any_edge   = 1;
        PIN_VSYNC_PORT.INTFLAGS = PIN_VSYNC_bm;
    }
}

/* ===================================================================
 * Field rate check (section 9)
 * ===================================================================
 *
 * The band is 45-65Hz nominal, CUT AT 43.5 AND 65.6. The margin is
 * there so a legitimate mode sitting on a boundary is not rejected over
 * a little measurement noise; without it a nominal 65Hz source that
 * measures 65.2 would be refused.
 *
 * ABSENT VSYNC PASSES. Some sources send Hsync alone, and a dongle that
 * blanked them would be broken for a case that works perfectly well --
 * the check exists to reject a field rate a CRT cannot follow, and no
 * field rate at all is not one of those.
 */
/* MEASURED IN QUARTER-MILLISECONDS FROM THE TICK, not by counting lines.
 *
 * Counting lines was the obvious choice -- the capture rides an accurate
 * 20MHz clock where the tick is only good to a fraction of a
 * millisecond -- and it was rejected twice, for different reasons.
 *
 * FIRST, because the count was taken by POLLING TCB0 in the main loop
 * and any pass slower than one line silently lost a capture. Missing 60
 * lines of 262 reads as 78.7Hz, outside the band, and the output
 * blanks. Not hypothetical: the loop is busiest during a DDC read, and
 * Windows polls DDC every second or two -- exactly the rate at which the
 * mode-valid pin was seen dropping out in bursts.
 *
 * SECOND, AND STILL TRUE NOW THAT v_line IS ADVANCED BY THE LEVEL 1
 * CAPTURE AND CANNOT LOSE A COUNT: v_frame_lines is not a field. On an
 * interlaced source only one field in two resets the counter -- see the
 * capture ISR, where that is deliberate, because the on-grid field's
 * Vsync edge races an Hsync -- so v_frame_lines is a whole FRAME. Using
 * it here would read 480i as 30Hz and blank every interlaced source.
 * Correcting it with a factor of two when v_ilace is set would make a
 * blanking decision depend on the interlace detector, which is a phase
 * heuristic with its own acquisition state. A safety check should not
 * import the failure modes of the machinery it is meant to protect.
 *
 * WHY QUARTER-MILLISECONDS AND NOT MILLISECONDS. field_period_q is the
 * difference of two counts, so a source whose true period is not a whole
 * number of them measures as one of the two integers either side, in
 * proportion to the fraction. That is harmless when the quantum is small
 * against the gap between the rates the threshold separates, and fatal
 * when it is not.
 *
 * On the old 1ms grid with the band at 45-75Hz it was harmless: 75Hz is
 * 13.33ms, read 13 or 14, and both passed. Narrowing the top to 65Hz
 * broke that, because 65Hz is 15.38ms and 70Hz is 14.29ms -- 1.1ms
 * apart, both straddling 15. Every frame at 70Hz read 14, 14, 14, 15,
 * and with two bad measurements to fail and one good one to recover
 * that is FORTY blank/unblank transitions per second. 70Hz is not
 * obscure; 640x350 and 720x400, the VGA text modes, are 31.5kHz at
 * 70Hz.
 *
 * TCF0 ALREADY INTERRUPTS AT 4kHz for the software PWM, so the finer
 * count is one uint16_t in an interrupt that was running anyway, and the
 * Vsync ISR reads it under the same level-0 rule that already covered
 * tick_count. Four counts now separate 65Hz from 70Hz where none did.
 *
 * A THRESHOLD ON A QUANTISED MEASUREMENT ALWAYS HAS A WINDOW AT EACH
 * EDGE where the reading dithers across it, and finer quanta move and
 * shrink that window without removing it:
 *
 *              top window            bottom window
 *   1ms        66.67-71.43Hz  4.76Hz    41.67-43.48Hz  1.81Hz
 *   0.25ms     65.57-66.67Hz  1.09Hz    43.01-43.48Hz  0.47Hz
 *
 * FIELD_MIN_Q = 61 rather than 60 places the top window at 65.57-66.67Hz
 * on purpose. 65Hz reads 61 or 62 and always passes; 66.67Hz reads
 * exactly 60 and always blanks; the window between them is empty of any
 * mode a monitor emits. 60 would put the edge at 66.67Hz and let Mac
 * 66.67Hz through, which is above the band that was asked for.
 *
 * WHAT THE WINDOW IS FOR IS SETTLED SEPARATELY, by the hysteresis at
 * field_rate_evaluate() -- the quanta decide WHERE the edge sits, the
 * hysteresis decides that a source sitting on it settles rather than
 * strobing. The two do different jobs and are worth keeping apart when
 * reading either. */
#define FIELD_MIN_Q        61U    /* 15.25ms -- 65.6Hz */
#define FIELD_MAX_Q        92U    /* 23.00ms -- 43.5Hz */

/* Two consecutive bad measurements before blanking. A single outlier --
 * a frame boundary landing either side of a tick, a source glitch --
 * must not blank a picture that is otherwise fine. */
#define FIELD_BAD_LIMIT    2

/* THE RECOVER EDGE SITS THIS MANY QUANTA INSIDE THE FAIL EDGE.
 *
 * One quantum is the whole of it. The measurement of any period reads
 * as one of the two integers either side of it and never further, so a
 * recover edge one quantum in cannot be satisfied by the same dither
 * that trips the fail edge. Two would widen the dead zone for nothing.
 *
 * Setting it to 0 restores the single-threshold rule exactly, which is
 * the A/B this wants on the bench. */
#define FIELD_HYST_Q       1U

_Static_assert(FIELD_MIN_Q + FIELD_HYST_Q <= FIELD_MAX_Q - FIELD_HYST_Q,
               "hysteresis has closed the recover band");


static void field_rate_evaluate(void)
{
    uint16_t q = field_period_q;

    if (!vsync_present || !q) {
        field_rate_ok = 1;
        field_bad     = 0;
        return;
    }

    /* STILL ASYMMETRIC IN TIME: two consecutive bad frames to fail, ONE
     * good frame to recover. Making that symmetric was tried with the
     * frame-length stability test and reverted with it -- it did not
     * help, and slowing recovery costs real time on every legitimate
     * mode change to fix nothing. Nothing below adds a frame of latency
     * to recovery; the first qualifying measurement still takes it.
     *
     * WHAT IS NEW IS HYSTERESIS IN VALUE RATHER THAN IN TIME. The fail
     * edge and the recover edge are different numbers, one quantum
     * apart, so which test a measurement has to satisfy depends on which
     * state the check is already in.
     *
     * WHY: the time asymmetry above is exactly what makes a measurement
     * sitting on the threshold STROBE instead of settling. A source at
     * the edge reads 60, 61, 60, 61; the 60s trip the fail edge and each
     * 61 immediately undoes it. Before the quarter-millisecond change
     * that was FORTY blank/unblank transitions per second at 70Hz. Finer
     * quanta moved the window somewhere no monitor mode lives, but a
     * threshold on a quantised measurement always has one, and moving a
     * fault is not fixing it.
     *
     * With the recover edge one quantum in, that same 60/61 dither can
     * satisfy the fail test and NEVER the recover test, so it blanks and
     * stays blanked. A dither one quantum higher satisfies neither fail
     * nor anything else, so it passes and stays passing. Either way it
     * settles. Swept 40-80Hz at 0.01Hz, worst case over 8000 frames goes
     * from 5308 transitions to one, and that one is the initial settle.
     *
     * WHAT IT COSTS, AND IT IS NOT NOTHING: one quantum at each edge is
     * a DEAD ZONE where the verdict depends on the direction the source
     * arrived from -- 64.52-65.57Hz at the top, 43.48-43.96Hz at the
     * bottom. A rate drifting DOWN into it stays passing; the same rate
     * arriving from outside stays blanked. That is what hysteresis means
     * and it is not a defect, but it is why the edges were placed where
     * they are: 65Hz reads 61 or 62, so it recovers from cold on the
     * first or second frame, and only a source at 65.57Hz exactly sits
     * deep enough in the zone to take seconds about it. Nothing emits
     * 65.57Hz.
     *
     * FIELD_HYST_Q = 0 collapses this back to the single-threshold rule
     * byte for byte, which is the comparison to make on the bench. */
    if (field_rate_ok) {
        if (q >= FIELD_MIN_Q && q <= FIELD_MAX_Q) {
            field_bad = 0;
        } else if (field_bad < FIELD_BAD_LIMIT
                && ++field_bad >= FIELD_BAD_LIMIT) {
            field_rate_ok = 0;
        }
    } else if (q >= (uint16_t)(FIELD_MIN_Q + FIELD_HYST_Q)
            && q <= (uint16_t)(FIELD_MAX_Q - FIELD_HYST_Q)) {
        field_bad     = 0;
        field_rate_ok = 1;
    }
}

static void update_vsync(uint16_t now)
{
    /* ONE path latches the frame, and it is the interrupt. The polled
     * edge detection that used to sit here has gone: with both running,
     * they disagreed about which frames had been counted. */
    if (vs_any_edge) {
        vs_any_edge   = 0;
        vs_change     = now;
        vsync_present = 1;
    }

    if (vs_frame_flag) {
        vs_frame_flag = 0;
        src_track_interlace(vs_phase);   /* deferred: neither is urgent */
        field_rate_evaluate();

        /* Fields alternate, so the one just processed names the next.
         * The Vsync ISR copies this alongside its request, because
         * parity needs the phase weighed against the line period and
         * that is not interrupt work. */
        v_next_is_mid = (uint8_t)(src_prev_mid ? 0 : 1);
        v_ilace_want  = src_interlaced;

        /* Mode FO reloads TCB1 once per field, but not from here -- the
         * one-shot may still be running. Armed now, serviced a couple of
         * milliseconds later. See fo_load_service(). */
        fo_load_pending = 1;
        fo_load_at      = now;
    }

    if (elapsed_since(now, vs_change) > 100) {
        vsync_present    = 0;
        field_period_q   = 0;
        field_rate_ok    = 1;          /* absent Vsync passes */
        src_interlaced   = 0;          /* nothing to be interlaced */
        src_alt_count    = 0;
        src_prog_count   = 0;
    }

}
static uint16_t pol_ref_period;
static uint8_t  pol_streak;


static uint16_t settle_start;
static uint16_t settle_len;
static uint8_t  settling;

/* ===================================================================
 * DDC / EDID client
 * ===================================================================
 *
 * Emulates the 24C02-style DDC EEPROM every VGA/HDMI source expects at
 * I2C address 0x50: a single-byte offset pointer set by a host write,
 * then sequential reads that wrap at 256 (free, since the offset is a
 * uint8_t).
 *
 * The served image is a 256-byte RAM shadow, rebuilt per mode from a
 * base plus a patch list -- see the block below, which is where that
 * scheme and its consequences are described.
 *
 * The E-DDC segment-pointer address 0x30 is also ACKed -- SADDRMASK in
 * ADDREN mode, which makes it a second exact address rather than a mask
 * -- with the segment byte accepted and discarded. Everything served
 * fits in segment 0, but some hosts write the segment pointer
 * unconditionally and sulk if it NACKs. Host writes to 0x50 beyond the
 * offset byte are likewise ACKed and discarded, matching how write-
 * protected DDC EEPROMs in real monitors behave; NACKing mid-write
 * upsets more hosts than silently ignoring does.
 */
#define DDC_EDID_ADDR     0x50
#define DDC_SEGMENT_ADDR  0x30

/* THE SIX EDIDs ARE THE SIX .bin FILES. THAT IS THE WHOLE SCHEME.
 *
 * This replaces a generated edid_data.h holding one base image plus
 * five patch lists. That was 605 bytes of flash against 1536 for six
 * raw images, and it was given up deliberately: the point of the change
 * is that an EDID can be edited in a hex editor or CRU, dropped into
 * the build directory under its existing name, and flashed, with no
 * generator step and no C to regenerate. 931 bytes at 40% utilisation
 * is what that costs.
 *
 * ONE REPRESENTATION, AND IT IS THE ONE THE BUILD EATS. edid_gen.py
 * emits the .bin files and nothing else now. §20.2 used to warn that a
 * second pipeline emitting a different representation would be a fork;
 * there is no longer a second representation for one to fork into.
 *
 * The images are pulled in by the assembler rather than by a header,
 * because .incbin needs no extra tool, no extra file, and -- unlike the
 * avr-objcopy -I binary route -- no architecture number in the
 * Makefile. Verified byte-identical: the 256 bytes at each symbol in
 * the .hex match the source .bin.
 *
 * The FULL 256 bytes are shadowed, not just the block Mode ED will
 * edit. A 128-byte shadow would put an "is this byte below 128?" test
 * on every byte served, inside an interrupt that is deliberately held
 * below the capture. 256 bytes of a 3KB SRAM buys the ISR staying
 * exactly as it was: one indexed load, no branch. */
#define EDID_BYTES  256

/* THE FILE NAMES ARE PART OF THE INTERFACE. They are baked in here, so
 * a replacement image must arrive under the same name or the build
 * fails at assembly time with `file not found: edidN.bin`.
 *
 * EACH FILE MUST BE 128 OR 256 BYTES, and the .if guards below enforce
 * it by name. This is not tidiness. edid_checksums() rewrites bytes 127
 * and 255 on every rebuild, so a truncated or overlong file would be
 * served as a plausible, correctly-checksummed, wrong EDID -- the
 * silent-wrong-artefact failure, arriving through the one door where
 * nothing else in this firmware would notice.
 *
 * A 128-BYTE FILE IS PADDED WITH THE CEA BLOCK THE SHIPPED IMAGES
 * CARRY: rev 3, no extension DTDs, basic audio, and an HDMI VSDB with
 * physical address 0.0.0.0. Byte 255 is emitted with the value that
 * checksums that block, which the firmware then recomputes anyway.
 *
 * WHAT PADDING IMPLIES, and it is a real change to what the dongle
 * advertises: a bare 128-byte EDID that declared no audio and no HDMI
 * vendor block will, after padding, declare both. That is the whole
 * point -- it is what makes an arbitrary drop-in look like the shipped
 * images to a host -- but it is not nothing, and a file that must NOT
 * advertise them has to arrive as 256 bytes carrying its own second
 * block.
 *
 * Byte 126 is fixed up at run time rather than here, because the
 * assembler can append bytes to included data but cannot alter it --
 * see edid_rebuild().
 *
 * WRITTEN OUT SIX TIMES ON PURPOSE. THE MACRO VERSION FAILED ON
 * WINDOWS AND BUILT CLEANLY ON LINUX. This was six lines once, an
 * `.macro EDID_IMAGE sym, file` taking the symbol and the filename and
 * substituting \\file into both the .incbin and the .error string. The
 * Linux assembler expanded it correctly, including the error path,
 * which is how it got shipped. The same binutils version on Windows
 * reported six bad escapes per invocation -- \\U \\B \\A \\L \\T \\c,
 * which is C:\\Users\\...\\AppData\\Local\\Temp\\cc*.s taken apart by the
 * string lexer. So the substitution was yielding the assembler's own
 * input filename rather than the argument, and only on that host.
 *
 * THE MECHANISM IS NOT UNDERSTOOD and no explanation is offered here,
 * because a wrong one would be worse than none: it may be that `file`
 * collides with something in that build, or that macro arguments are
 * bound differently there. What is certain is the shape of the fault
 * -- backslash substitution inside an assembler string, resolved by
 * the host -- so the fix is to have none. After this change the
 * emitted assembly for this block contains no backslash at all, which
 * is a property `make lst` can be grepped for and the reason the
 * remaining macro takes no arguments and contains no strings.
 *
 * THE COST OF THE VERSION THAT LOOKED BETTER was a build that only
 * worked on the machine it was tested on, in the one construct every
 * EDID in the product passes through. Six repeated blocks is the right
 * trade. */
__asm__ (
    ".section .rodata,\"a\",@progbits\n"

    /* Parameterless and string-free, deliberately -- see the note above
     * the images. This is the only macro left and it substitutes
     * nothing. */
    ".macro EDID_CEA_PAD\n"
    "  .byte 0x02, 0x03, 0x0E, 0x40\n"          /* CEA tag, rev 3, d=14, basic audio */
    "  .byte 0x23, 0x09, 0x7F, 0x07\n"          /* audio data block: LPCM, 2ch       */
    "  .byte 0x65, 0x03, 0x0C, 0x00, 0x00, 0x00\n" /* HDMI VSDB, phys addr 0.0.0.0   */
    "  .fill 113, 1, 0x00\n"                    /* d=14 means no extension DTDs      */
    "  .byte 0x87\n"                            /* block checksum; recomputed anyway */
    ".endm\n"

    "edid_img_1: .incbin \"EDID-Mode1.bin\"\n"
    ".if (. - edid_img_1) == 128\n"
    "  EDID_CEA_PAD\n"
    ".endif\n"
    ".if (. - edid_img_1) != 256\n"
    "  .error \"EDID-Mode1.bin must be 128 or 256 bytes\"\n"
    ".endif\n"
    ".global edid_img_1\n"

    "edid_img_2: .incbin \"EDID-Mode2.bin\"\n"
    ".if (. - edid_img_2) == 128\n"
    "  EDID_CEA_PAD\n"
    ".endif\n"
    ".if (. - edid_img_2) != 256\n"
    "  .error \"EDID-Mode2.bin must be 128 or 256 bytes\"\n"
    ".endif\n"
    ".global edid_img_2\n"

    "edid_img_3: .incbin \"EDID-Mode3.bin\"\n"
    ".if (. - edid_img_3) == 128\n"
    "  EDID_CEA_PAD\n"
    ".endif\n"
    ".if (. - edid_img_3) != 256\n"
    "  .error \"EDID-Mode3.bin must be 128 or 256 bytes\"\n"
    ".endif\n"
    ".global edid_img_3\n"

    "edid_img_4: .incbin \"EDID-Mode4.bin\"\n"
    ".if (. - edid_img_4) == 128\n"
    "  EDID_CEA_PAD\n"
    ".endif\n"
    ".if (. - edid_img_4) != 256\n"
    "  .error \"EDID-Mode4.bin must be 128 or 256 bytes\"\n"
    ".endif\n"
    ".global edid_img_4\n"

    "edid_img_5: .incbin \"EDID-Mode5.bin\"\n"
    ".if (. - edid_img_5) == 128\n"
    "  EDID_CEA_PAD\n"
    ".endif\n"
    ".if (. - edid_img_5) != 256\n"
    "  .error \"EDID-Mode5.bin must be 128 or 256 bytes\"\n"
    ".endif\n"
    ".global edid_img_5\n"

    "edid_img_S: .incbin \"EDID-ModeS.bin\"\n"
    ".if (. - edid_img_S) == 128\n"
    "  EDID_CEA_PAD\n"
    ".endif\n"
    ".if (. - edid_img_S) != 256\n"
    "  .error \"EDID-ModeS.bin must be 128 or 256 bytes\"\n"
    ".endif\n"
    ".global edid_img_S\n"

    ".text\n"
);

extern const uint8_t edid_img_1[], edid_img_2[], edid_img_3[],
                     edid_img_4[], edid_img_5[], edid_img_S[];

static uint8_t edid_shadow[EDID_BYTES];
static const uint8_t * volatile edid_image = edid_shadow;
static volatile uint8_t edid_offset;
static volatile uint8_t twi_is_segment;
static volatile uint8_t twi_expect_offset;
static volatile uint8_t twi_read_active;

/* Rebuild the shadow for `mode`. The caller must have the DDC client
 * disabled -- see edid_select().
 *
 * Both checksums are recomputed rather than trusted to the .bin. Mode
 * ED edits DTDs, so they have to be; and byte 126 is rewritten above,
 * which invalidates byte 127 on its own. Having the one code path that
 * produces a served image also produce its checksum is what keeps the
 * two from drifting.
 *
 * THE CONSEQUENCE FOR DROP-IN FILES, and it cuts both ways: a .bin does
 * not need a correct checksum, which makes hand-editing far easier;
 * and a corrupt one is served looking valid, which is why the size
 * guards in the .incbin block are the only check there is. */
/* Defined below, next to the rest of the DDC client. Declared here
 * because edid_select() has to take the client down across a rebuild
 * and the two live at opposite ends of this section. */
static void apply_edid_enable(void);
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
int main(void)
{
    clock_init();
    port_init();
    load_settings();

    evsys_init();
    ccl_configure(CCL_ROLE_PASSTHRU, pol_flip, h_pin_idle_high,
                  mode_valid, cs_hmode());

    /* THE RESUMED METHOD'S V HALF. load_settings() assigned cs_method
     * directly rather than through cs_set(), because at that point
     * there was no hardware to apply it to. This is the point where
     * there is: EVSYS is up, the port is configured, and pin 13 has to
     * start in the state the stored method asks for rather than in
     * whatever port_init() left it in. Without this a saved method 3
     * would come back with a dead pin 13 until the first method change
     * or offset nudge happened to re-route it. */
    v_pin_apply();
    tcb0_init();

    /* TCB1 HAS NEVER BEEN STARTED AT BOOT, and it should have been.
     *
     * It was only ever set up inside apply_role(), which returns early
     * when the role has not changed -- and ccl_role initialises to
     * PASSTHRU, which is the role boot configures. So on a source that
     * never changed role, TCB1 sat disabled forever, last_width_counts
     * stayed 0, and hoffset_apply() fell back to a sixteenth of the line
     * instead of the measured width section 6.4 asks for. It never
     * showed, because a sixteenth of a line is close to 4.7us at every
     * rate this serves -- and because the defence against reading CCMP
     * before the first capture made the symptom benign.
     *
     * One line, and the job owner has to be told what it is doing here
     * regardless, so this is where it goes. */
    tcb1_reevaluate();

    tcf0_init();

    /* Point the DDC client at the resumed mode's image before the
     * hardware could ACK anything, set the addresses up, then let
     * apply_edid_enable() decide from the resumed state whether the
     * client listens at all. */
    edid_select(current_mode);
    twi_client_init();
    apply_edid_enable();

    /* THE HSYNC CAPTURE IS THE ONE INTERRUPT THAT CANNOT BE LATE.
     *
     * TCB0 in frequency mode overwrites CCMP on every capture and leaves
     * CAPT set, so a handler delayed past one line -- 63.6us -- does not
     * merely arrive late, it loses that line entirely. Mode V counts
     * lines, and a lost count moves the emitted Vsync.
     *
     * At level 0 the handler queues behind every other interrupt, and
     * the TWI client is the one that matters: it is busiest during a DDC
     * read, which Windows performs every second or two, and that is
     * exactly when the mode-valid pin was seen dropping out in bursts.
     * Moving the capture out of the main loop and into an interrupt
     * removed the polling latency but not this one.
     *
     * Level 1 is the only priority that can preempt a level 0 handler,
     * and only one vector may hold it. This is the vector that earns it:
     * everything else here -- the tick, the Vsync edge, the button, the
     * TWI client -- tolerates tens of microseconds without consequence.
     *
     * Consequences, both handled above: this handler can now land inside
     * the Vsync ISR, so the frame boundary is passed to it as a flag
     * rather than being done there (see v_frame_req); and cli() still
     * blocks it, since only an NMI ignores the I bit -- which is why
     * ccl_configure() and ccl_set_polarity() may still lose a capture, and
     * why both run only inside a settle mute. */
    CPUINT.LVL1VEC = TCB0_INT_vect_num;

    sei();

    uint16_t start = now_ticks();
    last_hsync_tick = start;

    /* ONE CURTAIN OVER THE WHOLE OF ACQUISITION -- see
     * BOOT_SETTLE_TICKS. This is the only call that needs to change:
     * settle_begin_len() keeps whichever deadline is LONGER, so every
     * 40ms settle raised underneath it during acquisition is absorbed
     * rather than shortening it, and the settle cannot expire early
     * because the expiry test already refuses while pol_pending or
     * pol_measuring is set. */
    settle_begin_len(start, BOOT_SETTLE_TICKS);

    /* Section 8.1: the mode-and-profile report plays at power-on, so a
     * unit says what it is without being asked. On a locked unit this is
     * the only unprompted indication there will ever be. */
    report_mode_profile(start);

    while (1) {
        /* One tick sample per iteration, shared by everything below.
         * The loop has no blocking calls, so it runs many times per
         * millisecond and a single sample is as current as several. */
        uint16_t now = now_ticks();

        /* --- Hsync capture -------------------------------------- */
        if (cap_ready) {
            cap_ready = 0;
            /* Lock-free, and this one mattered more than the others.
             * It used to hold cli() across five memory accesses -- two
             * 16-bit loads, a store, and the flag clear -- which the
             * disassembly puts at about fifteen cycles, 750ns. Any Hsync
             * arriving inside that window had its phase sample delayed
             * by the whole of it, and 750ns is 15 counts, which is
             * precisely what the loop was reporting as its worst error.
             *
             * Read both values twice and retry if either moved. */
            uint16_t period = cap_period;

            last_period_counts = period;
            last_hsync_tick    = now;

            period_average(period);

            /* Shorter of the two halves is the sync pulse, whichever
             * polarity arrived. Read only when TCB1 IS ACTUALLY
             * MEASURING IT -- the timer now has three jobs, and CCMP in
             * the other two is a reshaping period or a field delay, both
             * of which would pass the sanity test below and quietly
             * corrupt the H reconstruction's pulse width. Asking the job
             * rather than the role is the difference between checking
             * what the timer is doing and inferring it. */
            if (tcb1_job == TCB1_JOB_WIDTH) {
                uint16_t hi = TCB1.CCMP;
                /* hi == 0 must be rejected, not just hi >= period.
                 * TCB1 reads zero before its first completed capture,
                 * and zero passed the old test: min(0, period) is 0, so
                 * last_width_counts became 0 and the emitted pulse
                 * clamped to its 1us floor. A 1us pulse where the source
                 * sends 4.7us is not a sync pulse a separator handles
                 * well, and it would show as a picture displaced by a
                 * fixed amount with the edges unstable -- regardless of
                 * anything the offset did. */
                if (hi > 0 && hi < period) {
                    uint16_t lo = (uint16_t)(period - hi);
                    last_width_counts = (hi < lo) ? hi : lo;
                }
            }

            /* Modeline change by period step: more than ~1.6% for eight
             * consecutive lines.
             *
             * pol_ref_period == 0 means there is no reference yet --
             * at start-up, and after every dropout, where the watchdog
             * clears it. Adopt the period silently rather than
             * comparing against zero, which would otherwise read as a
             * 100% step and manufacture a modeline change out of the
             * first eight captures back. The watchdog has already
             * asked for a polarity re-measure in that case, so the
             * streak would have been redundant as well as wrong. */
            if (pol_ref_period == 0) {
                pol_ref_period = period;
                pol_streak     = 0;
            } else {
                uint16_t dp = (period > pol_ref_period)
                            ? (uint16_t)(period - pol_ref_period)
                            : (uint16_t)(pol_ref_period - period);
                if (dp > (period >> POL_PERIOD_SHIFT)) {
                    if (pol_streak < POL_STREAK_REQUIRED) pol_streak++;
                    if (pol_streak >= POL_STREAK_REQUIRED) {
                        pol_ref_period = period;
                        pol_streak     = 0;
                        pol_pending       = 1;
                        width_pending     = 1;  /* new modeline, new width */
                        genlock_reacquire = 1;
                        /* THE LONG ONE. A card changing modeline does
                         * not go straight there: it emits genuinely
                         * stable intermediate modes for tens of
                         * milliseconds each, and where those land in an
                         * accepted window -- Modes 3 and 5 take 15, 25
                         * and 31kHz -- the unit correctly reports a
                         * valid source and unmutes into it. Measured at
                         * 100ms coming down from 31kHz and 200ms going
                         * up.
                         *
                         * Nothing in the signal separates a stable
                         * intermediate 25kHz from a real 25kHz source,
                         * because it IS one. A stability test was tried
                         * and reverted; see hsync_valid below. So this
                         * is a timer, knowingly, and it is the only
                         * mechanism left.
                         *
                         * It retriggers on each step, so the mute runs
                         * from the LAST one rather than the first and
                         * a slower card is covered without a longer
                         * constant. */
                        settle_begin_len(now, SETTLE_TICKS_SOURCE);
                    }
                } else {
                    pol_streak = 0;
                }
            }

            uint8_t windows = 0;
            if (period >= HSYNC_FAST_MIN_COUNTS
             && period <= HSYNC_FAST_MAX_COUNTS) windows |= W_FAST;
            if (period >= HSYNC_SLOW_MIN_COUNTS
             && period <= HSYNC_SLOW_MAX_COUNTS) windows |= W_SLOW;
            if (period >= HSYNC_M4_MIN_COUNTS
             && period <= HSYNC_M4_MAX_COUNTS)   windows |= W_M4;

            /* Computed straight from this period's window check, mode
             * by mode, with no smoothing or debounce on top. An earlier
             * ATtiny824 revision added hysteresis and then a longer-
             * timescale block mechanism to smooth boundary flicker on
             * Mode 4's narrow window; each layer fixed the failure mode
             * it targeted and was immediately followed by a new one at
             * a different timescale. It was fully reverted. */
            last_windows = windows;
            /* Inside an adjustment mode the acceptance window comes
             * from MODE_5, not from the mode being adjusted.
             *
             * Mode S normally accepts 15kHz and 31kHz and divides the
             * fast one, which is right for Mode S itself -- but an
             * adjustment mode is a place you sit and watch a picture
             * while turning a control, and a source that drifts out of
             * the window mid-adjustment would blank the very picture
             * being adjusted. MODE_5 accepts all three windows, so the
             * picture stays up. Applies to Mode V and Mode FO too when
             * they arrive, and to anything else added inside Mode S. */
            /* MODE CS KEEPS THE NUMBERED MODE'S WINDOW; the other
             * adjustment modes widen to Mode 5's.
             *
             * Widening is right for H, V and FO: you are tuning an
             * offset and the picture has to be visible while you do it,
             * which is the same reasoning behind the ui_state guard on
             * the DIVIDE role above.
             *
             * It is wrong for Mode CS, because a combine method is a
             * property OF the mode it was chosen in. Widening would
             * bring a source outside Mode 4's window on screen while
             * the user picks a method for it, then drop it again on
             * exit -- the method validated against a window it will
             * never run in. Mode ED widens and is deliberately left
             * doing so: it edits EDID rather than sync behaviour, so
             * the argument does not carry across. */
            uint8_t win = (ui_state == UI_NORMAL || ui_state == UI_ADJ_CS)
                            ? mode_windows[current_mode]
                            : mode_windows[MODE_5];
            /* MEMBERSHIP ONLY. A stability test was tried here and
             * reverted: the same tolerance and streak the step detector
             * uses, inverted to mean "the rate has stopped moving",
             * gating the valid direction.
             *
             * It made no difference, which says the premise was wrong.
             * The card is not sweeping continuously through 25kHz on
             * its way to 31kHz -- if it were, no streak could form and
             * the test would have worked. It is far more likely to be
             * emitting genuinely stable intermediate modes for tens of
             * milliseconds each, and a stable 25kHz signal is
             * indistinguishable from a real 25kHz source because that
             * is exactly what it is. No amount of looking at the
             * signal separates them.
             *
             * Which leaves only a timer -- ignore everything for N ms
             * after a change -- and that is the block mechanism the
             * ATtiny824 grew and then reverted, described three lines
             * above. Not adding it a second time. */
            hsync_valid = (windows & win) ? 1 : 0;

            /* Only act on a window the current mode actually accepts.
             * Deciding the role from an unaccepted window would have
             * Mode S engage the divider for a source it is about to
             * mute anyway. */
            /* HIDDEN BY THE BOOT CURTAIN, NOT FIXED -- do not let this
         * stand as evidence the ordering is right.
         *
         * hoffset_start() runs BELOW this call, so on the first good
         * capture after reset or a dropout hoffset_running is still 0
         * and role_wanted() returns PASSTHRU. The role only reaches
         * RECON on a later pass, from the H-offset block further down.
         *
         * The cost is not the capture of latency it looks like. The
         * first polarity measurement takes 20ms, and the role is still
         * moving while it runs -- so want_flip gets computed against a
         * transient role, then recomputed against the settled one, and
         * each answer raises its own settle. That was the boot strobe.
         * BOOT_SETTLE_TICKS covers it; the ordering is still wrong.
         *
         * Reordering means starting the H offset before the role that
         * consumes it is chosen, which is a change to working
         * acquisition code and wants its own increment and its own
         * bench round. */
        if (hsync_valid) apply_role(role_wanted(windows), now);

            /* Acquire on the first good line, then never restart. A
             * modeline change arrives as a period step, which the block
             * above has already flagged -- and that is the one event
             * that justifies re-acquiring, because the line rate itself
             * has moved. A role change is not: the rate is unchanged
             * and the loop has nothing to relearn. */
            if (hsync_valid && !hoffset_running) hoffset_start(period);
            else if (hoffset_running && genlock_reacquire) {
                /* Only a genuine rate change matters now, and only
                 * because the offset step and the pulse width are
                 * scaled from the measured period. */
                genlock_reacquire = 0;
                period_avg_ok = 0;          /* the rate moved: start over */
                period_average(period);
                hoffset_apply(period_best_hires());
            }
        }

        /* --- H offset: re-place the pulse when the setting moves - */
        /* The offset is a setting, not a per-line quantity: the
         * hardware places every pulse from CMP0 and CMP1 without help,
         * so these only need rewriting when the setting changes. */
        if (hoffset_running) {
            static uint8_t last_off = 0xFF;

            if (last_off != h_offset) {
                last_off = h_offset;
                hoffset_apply(period_best_hires());
                apply_role(role_wanted(last_windows), now);
            }

            /* NO PERIOD REFRESH, and the measurement is why.
             *
             * Re-applying the negative side's placement as the averaged
             * period moved was measured at 180ns of edge spread against
             * 110ns with it frozen. Every rewrite moves the pulse, and
             * moving it more often does not make the moves smaller --
             * it just adds a second source of displacement on top of
             * whatever the first one was.
             *
             * The average is still used, once, for the placement made
             * at acquisition and on each offset change: a single
             * capture is quantised to a whole count and can be 25ns
             * wrong, where the average is good to about 3ns. That is a
             * static accuracy gain and costs nothing. What does not
             * work is treating it as something to track.
             *
             * The rejected refresh was kept for a while as an
             * `else if (0)` branch. The compiler discarded it, so it
             * cost nothing to run and everything to read: a reader has
             * to work out that the condition is a constant before they
             * can stop reasoning about when it fires. The reasoning is
             * worth keeping; the code was not. */
        }

        /* --- Sync watchdog -------------------------------------- */
        /* HSYNC_WATCHDOG_TICKS being too small is not a mild problem,
         * because a false watchdog does two things that compound. It
         * re-arms the polarity measurement, and it clears the reference
         * period. The cleared reference then reads as a 100% step on
         * every following capture, so the eight-line streak completes
         * in half a millisecond and calls settle_begin(), which starts
         * a 40ms mute. Fire the watchdog once per millisecond and that
         * mute is restarted forty times before it can expire: Csync is
         * muted permanently, mode-valid never goes high, and the whole
         * thing looks like a source that is never accepted. */
        if (elapsed_since(now, last_hsync_tick) >= HSYNC_WATCHDOG_TICKS) {
            if (hsync_valid) {
                hsync_valid = 0;
                settle_begin(now);
            }
            /* Fall back to pass-through while there is no source. The
             * divider would otherwise sit clocked by a dead pin, and
             * whatever level the flip-flop stopped at would be frozen
             * into the combiner. Pass-through leaves the array in the
             * shape the next source is most likely to want, and
             * role_wanted() puts the divider back if it is a fast one. */
            apply_role(CCL_ROLE_PASSTHRU, now);
            hoffset_stop();
            /* A dropout is the reliable announcement of a modeline
             * change: a GPU reprogramming its PLL always drops sync.
             * Arm the re-measure for whenever captures come back. */
            pol_pending       = 1;
            width_pending     = 1;  /* sync went away; re-measure it */
            genlock_reacquire = 1;
            pol_ref_period    = 0;
        }

        /* --- Polarity ------------------------------------------- */
        if (elapsed_since(now, pol_recheck_at) >= POL_RECHECK_MS) {
            pol_recheck_at = now;
            pol_recheck    = 1;
        }

        if ((pol_pending || pol_recheck) && hsync_valid) {
            polarity_measure(now);
        } else if (pol_measuring && !hsync_valid) {
            /* Abandoned rather than guessed: with no Hsync arriving
             * there is nothing to measure against. */
            pol_measuring = 0;
        }

        /* --- Output gating -------------------------------------- */
        /* THE SETTLE DOES NOT EXPIRE WHILE A POLARITY DECISION IS
         * STILL OUTSTANDING.
         *
         * A modeline change fires the period-step streak, which arms
         * this settle AND asks for a polarity re-measure. The settle is
         * a fixed 40ms from the disturbance; the measurement cannot
         * start until Hsync comes back in-window, and takes 20ms once
         * it does. On a source that takes its time returning, the timer
         * runs out first and the output unmutes into the middle of an
         * unfinished decision -- then mutes again when the answer
         * arrives and the truth tables are rewritten.
         *
         * Two mutes with a live gap between them, from one event. The
         * gap is the defect, not either mute.
         *
         * Holding the settle open bounds it by the decision rather than
         * by a guessed duration, so there is no constant to tune and no
         * source too slow for it. It cannot hang: pol_measuring is
         * abandoned above when Hsync goes away, and pol_pending only
         * keeps the mute up while hsync_valid is false, which is muting
         * the output anyway. */
        if (settling && !pol_pending && !pol_measuring
         && elapsed_since(now, settle_start) >= settle_len) {
            settling = 0;
        }
        /* Csync is gated on the field rate too. A rate a CRT cannot
         * follow is worse than no output: the set hunts, and on some
         * older monitors that is not merely ugly. Blanking says
         * plainly that this source will not work here. */
        set_mode_valid(hsync_valid && field_rate_ok
                       && !settling && !pol_pending);

        /* --- Vsync presence, for the sync report ----------------- */
        update_vsync(now);

        /* --- Button --------------------------------------------- */
        update_b1(now);

        /* --- Deferred single press in MS (section 8.2) ----------- */
        if (ms_press_pending
         && elapsed_since(now, ms_press_at) >= MS_DOUBLE_MS) {
            ms_press_pending = 0;
            change_mode(MODE_1, now);
            report_mode_profile(now);
        }

        /* --- Mode V: substitute the regenerated Vsync ------------
         *
         * Only when the offset is off centre AND a frame length is
         * known, so a unit that has never seen a complete frame cannot
         * emit a Vsync from a guess. At centre the pin is handed back
         * and the source passes through untouched.
         *
         * INTERLACED SOURCES ARE NOW SERVED, not refused. The count is
         * referenced to one field per frame and two pulses are emitted
         * from it, the second carrying half a line from Mode FO's
         * one-shot. The frame length matters more than it used to --
         * it now places the second pulse as well as the negative
         * offsets -- which is why the test on it stays. */
        v_set_source(v_offset != V_OFFSET_DEFAULT && v_frame_lines
                     && vsync_present);

        /* --- Mode FO: the per-field delay ------------------------
         *
         * Same argument in the mirror. Engaged only on an interlaced
         * source, off centre, with a measured line period to scale the
         * delay from -- and it stands down for the polarity window's
         * width burst, which wants TCB1 back. */
        fo_update();
        fo_load_service(now);

        /* --- Lockout, and its repeating refusal ------------------- */
        cannot_help_on = adj_locked_out();

        /* TRUNCATED THE INSTANT THE SOURCE BECOMES USABLE.
         *
         * The refusal runs 4.3 seconds. Letting it finish after the
         * condition has cleared means up to four seconds of a control
         * saying "I cannot help" while it can, in fact, help -- and the
         * obvious thing to do during those four seconds is press the
         * button, which now works, so the picture moves while the LED
         * insists nothing is happening. Contradicting itself is worse
         * than either message alone.
         *
         * Only the refusal is cut. cannot_help_playing marks the urgent
         * player as carrying THIS pattern, so a future urgent user is
         * not silently truncated by a condition that has nothing to do
         * with it. Nothing is played in its place: blink_service clears
         * the pin on the same pass, and in Mode FO the rate blink picks
         * it up on the next one. */
        if (!cannot_help_on && cannot_help_playing) {
            cannot_help_playing = 0;
            urgent_active       = 0;
        }

        if (cannot_help_on && !b1_pressed && !blink_busy()
         && elapsed_since(now, cannot_help_at) >= ADJ_STROBE_MS) {
            /* The gap between repeats is the 1200ms of dark at the end
             * of the pattern itself, so waiting for the player to go
             * idle is enough. The elapsed test only matters at the
             * moment the mode opens, where cannot_help_at is seeded with
             * the entry time: that buys one gap's grace before the first
             * refusal, which the interlace detector -- four alternations,
             * four frames, under 70ms -- comfortably fits inside. An
             * interlaced source is never accused of being progressive
             * merely for not having been measured yet.
             *
             * Suppressed while B1 is down because the hold preview owns
             * the LED then, and a refusal fired underneath it would be
             * invisible and would have consumed its own repeat slot. */
            cannot_help_at      = now;
            cannot_help_playing = 1;
            blink_urgent(pat_cannot_help,
                         (uint8_t)(sizeof pat_cannot_help / 2), now);
        }

        /* --- Strobe expiry ---------------------------------------
         *
         * The strobe has to time out on its own, not merely when the
         * next press arrives. It was cleared only inside b1_release, so
         * after a landmark the flag stayed set indefinitely -- and
         * because the LED block suppresses the hold preview while it is
         * set, every subsequent hold went dark. The actions still ran;
         * only the indication vanished, which made a working control
         * look dead. */
        if (adj_strobing
         && elapsed_since(now, adj_strobe_at) >= ADJ_STROBE_MS) {
            adj_strobing = 0;
        }

        /* --- Adjustment mode idle timeout (section 8.3) ---------- */

        /* A HELD BUTTON IS ACTIVITY. adj_last_input is written only on
         * RELEASE -- at the top of the adjustment branch of
         * b1_release(), and on entry to each mode. Both are release
         * events, so without the !b1_pressed term a hold that spans the
         * deadline fires the discard MID-PRESS, and the damage is not
         * confined to the discard:
         *
         * In Mode H at 19s, press and hold intending a 4s save. At 20s
         * this block reverts h_offset to adj_entry and sets ui_state to
         * UI_NORMAL. At 4s the button comes up, and b1_release() no
         * longer takes the adjustment branch -- ui_state says NORMAL --
         * so it falls into the Mode S table instead, where held >=
         * HOLD_MODE_V_MS lands the user in MODE V with the H offset
         * silently thrown away. The save gesture became a mode change.
         *
         * The release path refreshes adj_last_input itself, so holding
         * the timeout off while the button is down is the whole fix;
         * the countdown restarts from the release. */
        if (ui_state != UI_NORMAL
         && !b1_pressed
         && elapsed_since(now, adj_last_input)
            >= ((ui_state == UI_ADJ_ED) ? ED_IDLE_MS : ADJ_IDLE_MS)) {
            /* Discard: walking away must not commit a half-made change,
             * and the unit is left where it was rather than where it was
             * being dragged to.
             *
             * Mode ED gets 30s rather than 20s, and discards BOTH axes
             * -- the same argument as saving both. The re-render is not
             * optional: ed_pos and ed_size have been driving the served
             * EDID all the way through the session, so putting the
             * variables back without rebuilding would leave the shadow
             * holding the abandoned geometry. Live state and stored
             * state, together, in one breath -- section 19.2. */
            if (ui_state == UI_ADJ_ED) {
                ed_pos  = ed_entry_pos;
                ed_size = ed_entry_size;
                edid_select(current_mode);
            } else if (ui_state == UI_ADJ_CS) {
                /* Through cs_set(), so the truth table goes back with
                 * the variable. Assigning cs_method here would leave
                 * pin 12 in the abandoned method with the setting
                 * saying otherwise -- the same shape as leaving the
                 * EDID shadow holding abandoned geometry, three lines
                 * up. And it must be tested BEFORE the else: adj_cur()
                 * has no row for UI_ADJ_CS and the store below would be
                 * through a null pointer. */
                cs_set(cs_entry, now);
                cs_report_n = 0;
            } else {
                *adj_cur()->value = adj_entry;
            }
            ui_state = UI_NORMAL;
            report_mode_profile(now);
        }

        /* --- Sync report (section 8.2) --------------------------- */
        if (current_mode == MODE_S && ui_state == UI_NORMAL && !b1_pressed) {
            /* A free-running cycle rather than a timer armed by the
             * fault, so one mechanism reports both failure and recovery.
             * Any button edge restarts it, so a report cannot land on
             * top of another pattern. */
            static uint16_t sync_at;
            if (elapsed_since(now, b1_edge_at) < 5000) {
                sync_at = now;
            } else if (elapsed_since(now, sync_at) >= 5000) {
                sync_at = now;
                if (!blink_busy()) play_sync_report(now);
            }
        }

        /* THE BLINK LED, PIN 5, HAS FIVE CLAIMANTS. In order,
         * strongest first:
         *
         *   1  the hold preview, while B1 is down. It has to say what
         *      releasing at this instant will do, and nothing else may
         *      interrupt that.
         *   2  the cannot-help refusal, on the urgent player.
         *   3  the 1200ms landmark strobes, on the normal player.
         *   4  Mode FO's rate blink, which is the background state of
         *      that mode and yields to everything.
         *   5  Mode CS's method count, which is a brightness curve
         *      rather than a pattern and so cannot be held by the blink
         *      engine either.
         *
         * The CS report tests cs_report_n INSTEAD of blink_busy(), and
         * the difference is deliberate. The rate blinks are a
         * background state with no end, so they must stand aside for
         * any pattern that wants to play. The CS report is a finite
         * answer to a press that has just happened, it stopped the
         * players itself when it started, and it is the ONLY indication
         * that mode has -- deferring it to a pattern would mean the
         * user pressed the button and nothing happened. It also needs
         * no cannot_help_on term: Mode CS has no lockout, and
         * adj_locked_out() is not given a case for it.
         *
         * cs_report_n is left set on exit rather than cleared. It is
         * only ever read while ui_state is UI_ADJ_CS, and entry always
         * calls cs_report_start(), so a stale count cannot be reached.
         *
         * The rate blink is tested against both players rather than
         * being folded into the blink engine, because it is not a
         * pattern: it has no end, and a player that never finishes would
         * block every pattern behind it forever. */
        if (b1_pressed && !adj_strobing)
            hold_preview(elapsed_since(now, b1_down), now);
        else if (ui_state == UI_ADJ_FO && !cannot_help_on && !blink_busy())
            fo_rate_blink(now);
        else if (ui_state == UI_ADJ_ED && !cannot_help_on && !blink_busy())
            ed_rate_blink(now);
        else if (ui_state == UI_ADJ_CS && cs_report_n)
            cs_report_run(now);
        else
            blink_service(now);
    }
}
